spitzlbergerj/CaravanPi/circuit-board/V5/README.md

Die Dateien für die Bestellung bei JLCPCB.com sind im Verzeichnis JLCPCB enthalten

# Verkabelung zum Raspberry Pi

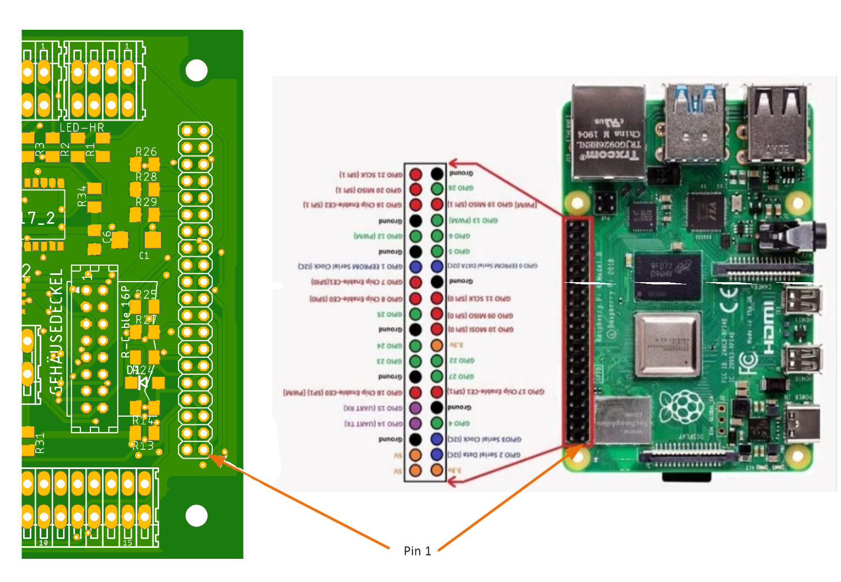
[picture p18: circuit-board/V5/CaravanPiPlatine-V5-Verbindung-RPi.png]
Verkabelung
