spitzlbergerj/CaravanPi/circuit-board/V3/README.md

# Platine Version 3

Diese Platinen-Version nutzt SMD Bauteile für alle Widerstände, Kondensatoren, Dioden und ICs **mit Ausnahme des P82B715P I2C Extender Chips**. Dieser ist hier als bedrahtete Version vorgesehen

## Platinen Layout
Oberseite  
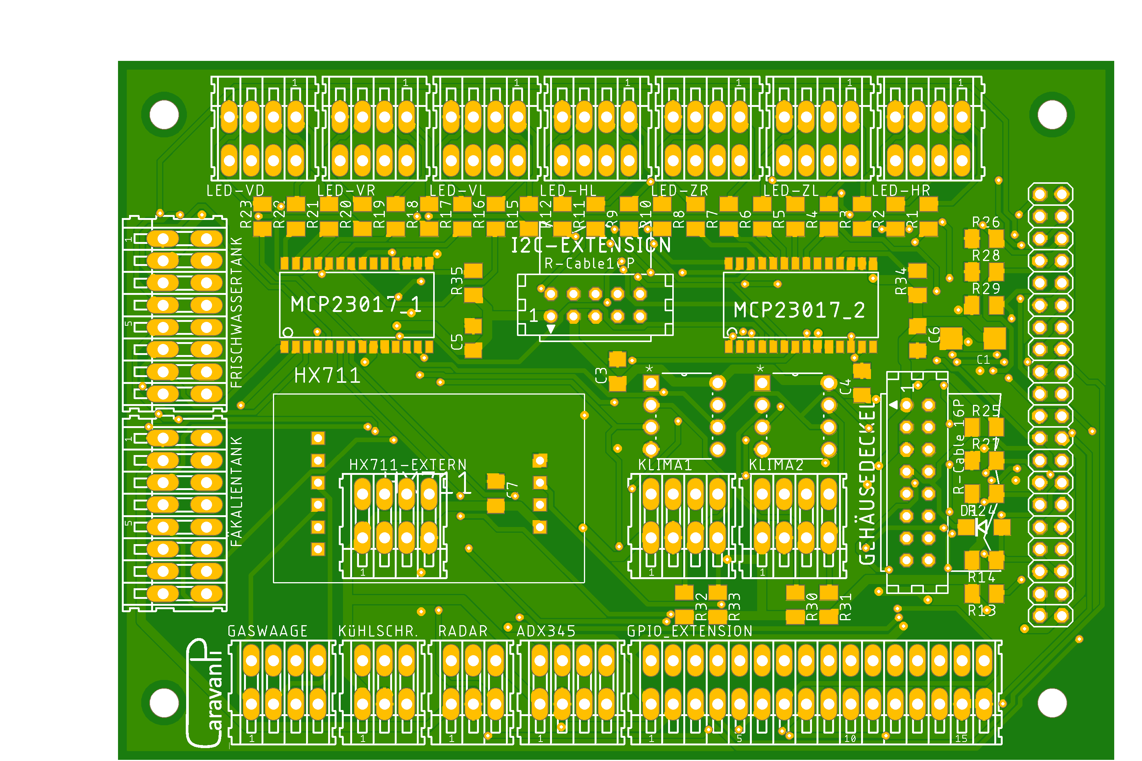
[picture p19: circuit-board/V3/CaravanPi-Platine-V3-Oberseite.png]
CaravanPi Platine V3 Oberseite
  

Unterseite  
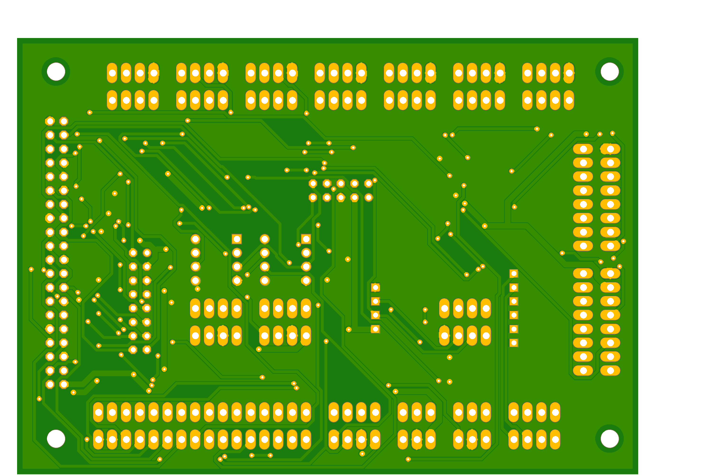
[picture p20: circuit-board/V3/CaravanPi-Platine-V3-Unterseite.png]
CaravanPi Platine V3 Unterseite
  

Bestückungslayout  
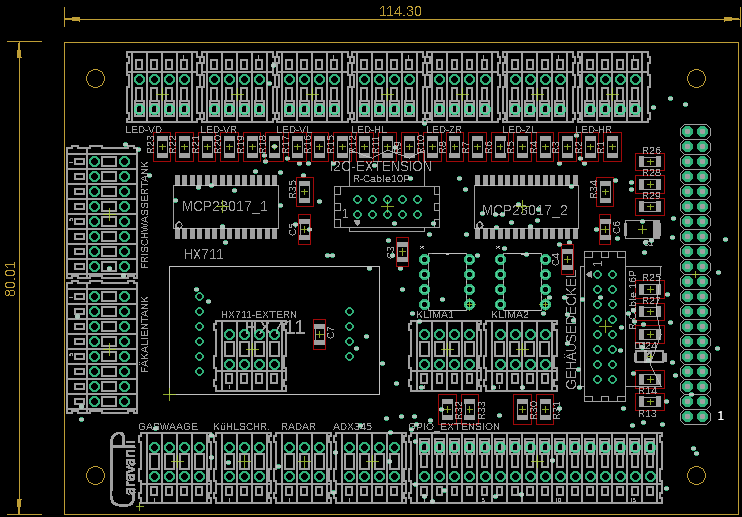
[picture p21: circuit-board/V3/CaravanPi-Platine-V3-Layout1.png]
CaravanPi Platine V3 Bestückungslayout
  

Bohrungen  
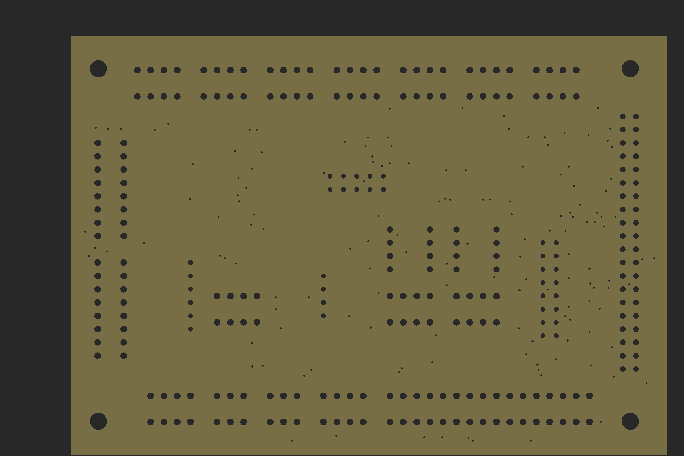
[picture p22: circuit-board/V3/CaravanPi-Platine-V3-Bohrungen.png]
CaravanPi Platine V3 Bohrungen
  

## Handbestückte Platine - Platine gefertigt in EU

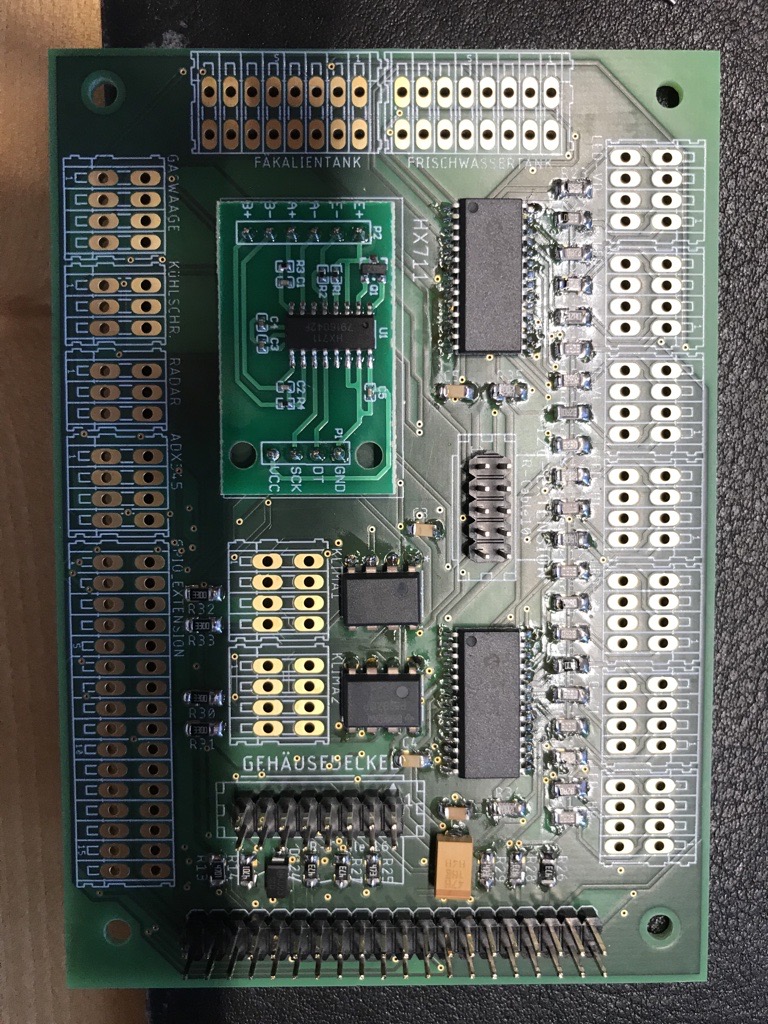
[picture p23: circuit-board/V3/CaravanPi-Platine-V3-EU-SMD-bestueckt.jpg]
CaravanPi Platine V3 EU per Hand bestückt
  

## JLCPCB Platine maschinell bestückt

CaravanPi Platine JLCPCB SMT bestückt  

Alle für die Bestellung bei JLCPCB.com benötigten dateien finden Sie im Unterverzeichnis [JLCPCB](JLCPCB)

## Bauteile Liste
In der Exceltabelle finden Sie alle benötigten Bauteile
