spitzlbergerj/CaravanPi/circuit-board/V4/README.md

# Platine Version 4

Diese Platinen Version nutzt SMD Bauteile für alle Widerstände, Kondensatoren, Dioden und ICs inkl. P82B715P I2C Extender Chips. Damit kann diese Platinenversion z. B. bei JLCPCB vollständig gefertigt werden, so dass nur noch Stecker und Klemmen manuell gelötet werden müssen.

## Platinen Layout
Oberseite  
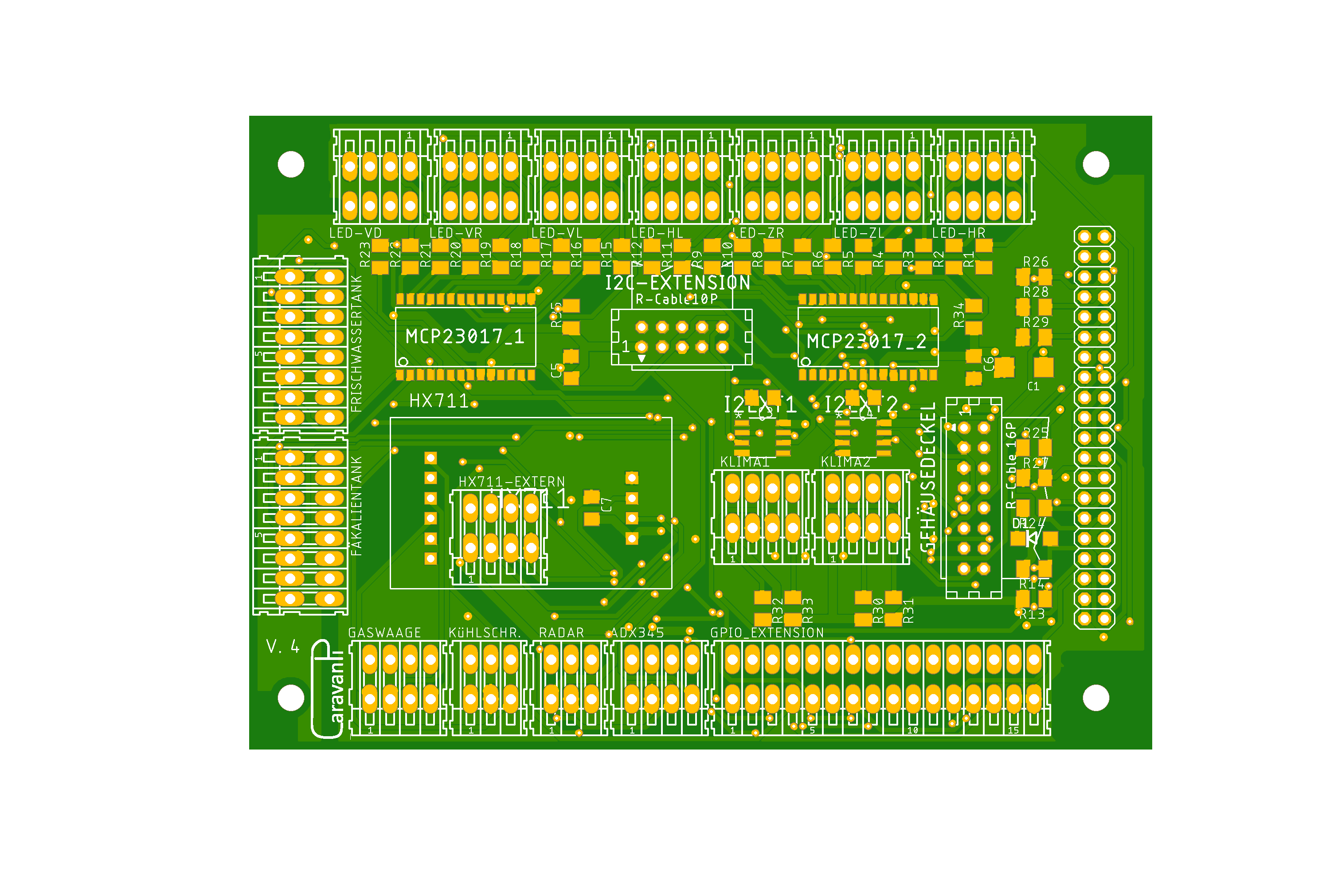
[picture p24: circuit-board/V4/CaravanPi-Platine-V4-Vorderseite.png]
CaravanPi Platine V4 Oberseite
  

Unterseite  
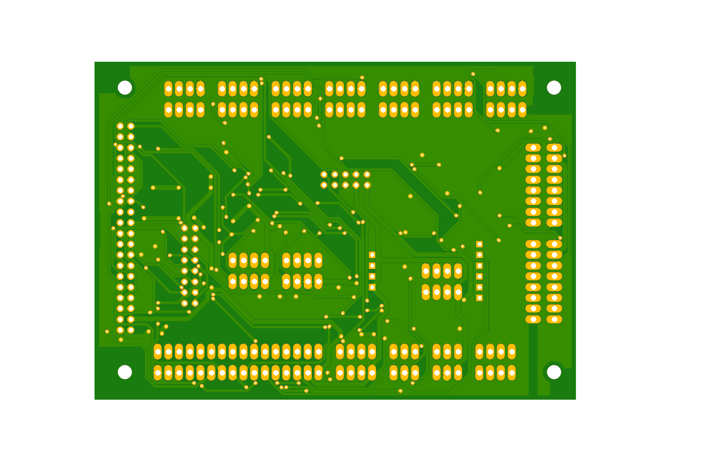
[picture p25: circuit-board/V4/CaravanPi-Platine-V4-Rueckseite.png]
CaravanPi Platine V4 Unterseite
  

Bestückungslayout  
CaravanPi Platine V4 Bestückungslayout  

Bohrungen  
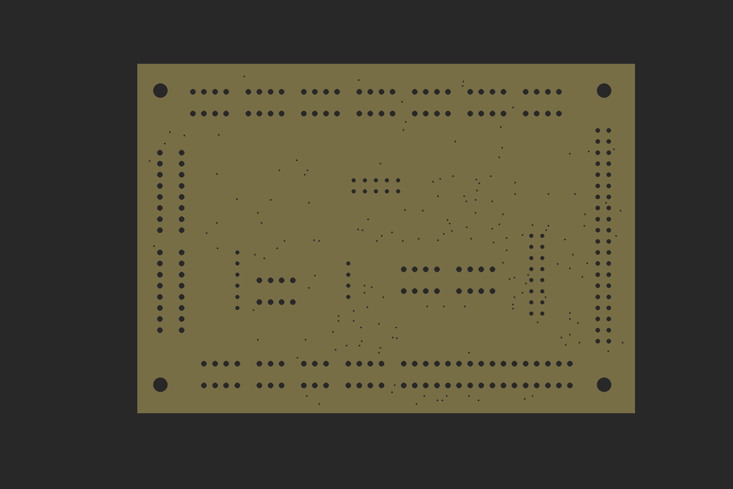
[picture p26: circuit-board/V4/CaravanPi-Platine-V4-Bohrungen.png]
CaravanPi Platine V4 Bohrungen
  

## JLCPCB Platine maschinell bestückt

CaravanPi Platine JLCPCB SMT bestückt  

Alle für die Bestellung bei JLCPCB.com benötigten dateien finden Sie im Unterverzeichnis [JLCPCB](JLCPCB)

## Bauteile Liste
In der Exceltabelle finden Sie alle benötigten Bauteile
