spitzlbergerj/CaravanPi/circuit-board/V5/JLCPCB/README.md

Dateien für die Bestellung bei JLCPCB.com

Teile Liste Stand 19.02.2023, inzwischen geändert, siehe neuestes BOM File

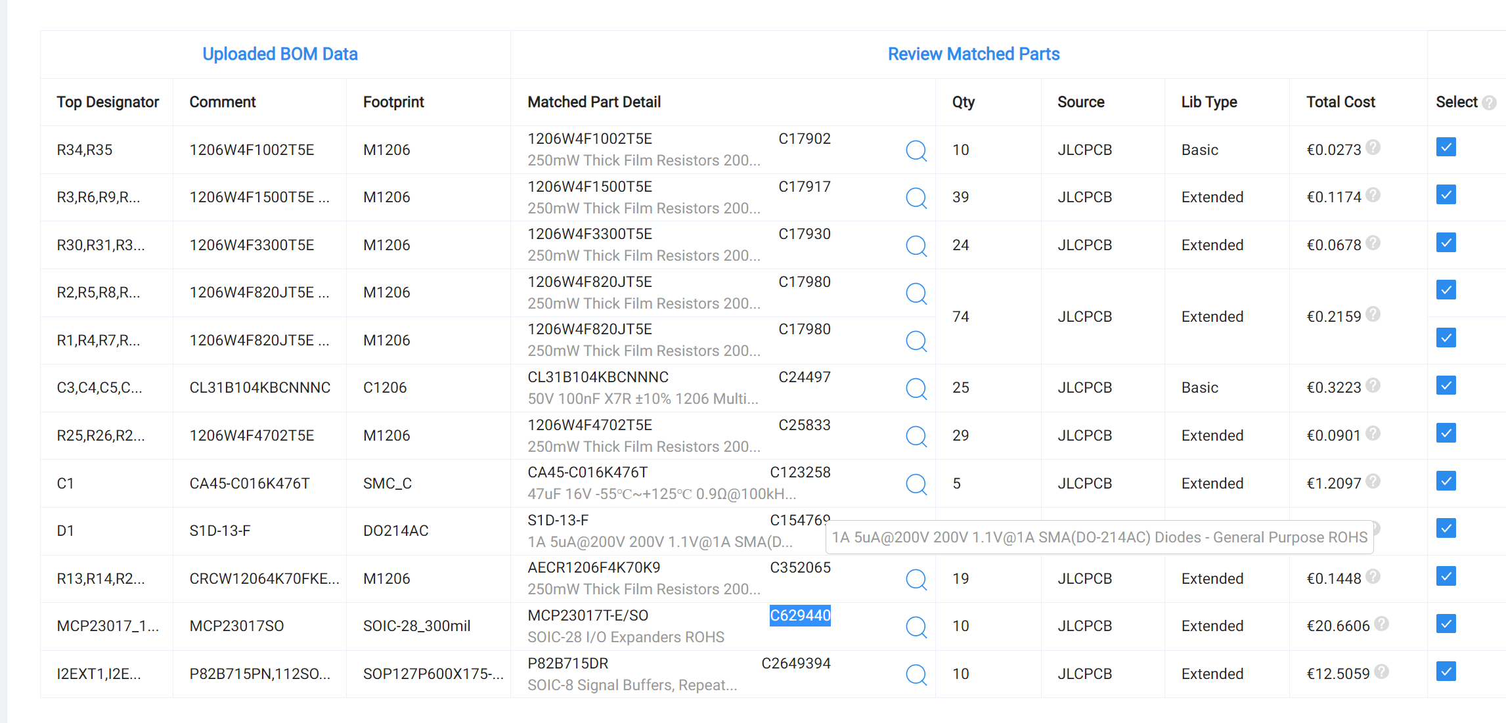
[picture p27: circuit-board/V5/JLCPCB/part-List-2023-02-23 083711.png]
 

Positionierung auf Platine

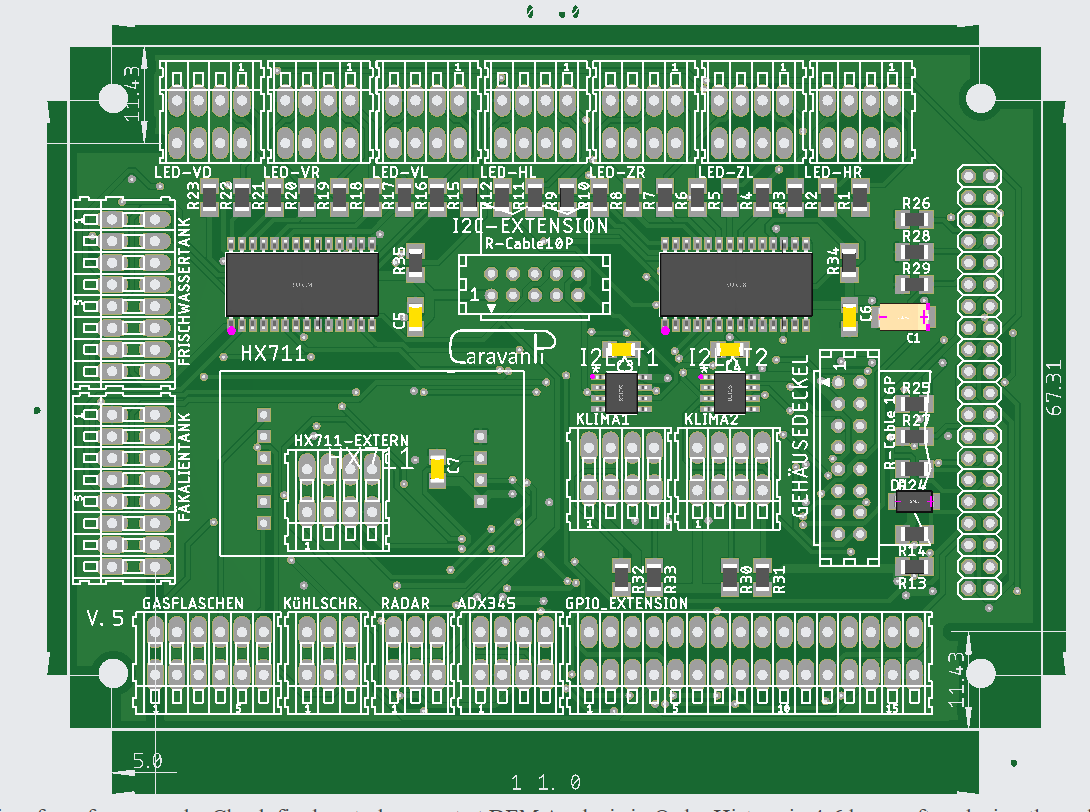
[picture p28: circuit-board/V5/JLCPCB/part-placement-2023-04-11.png]
