spitzlbergerj/CaravanPi/circuit-board/V3/JLCPCB/README.md

Dateien für die bestellung einer SMT bestückten Platine bei JLCPCB.com
