spitzlbergerj/CaravanPi/CaravanPi-Gesamt-Schaltplan.png

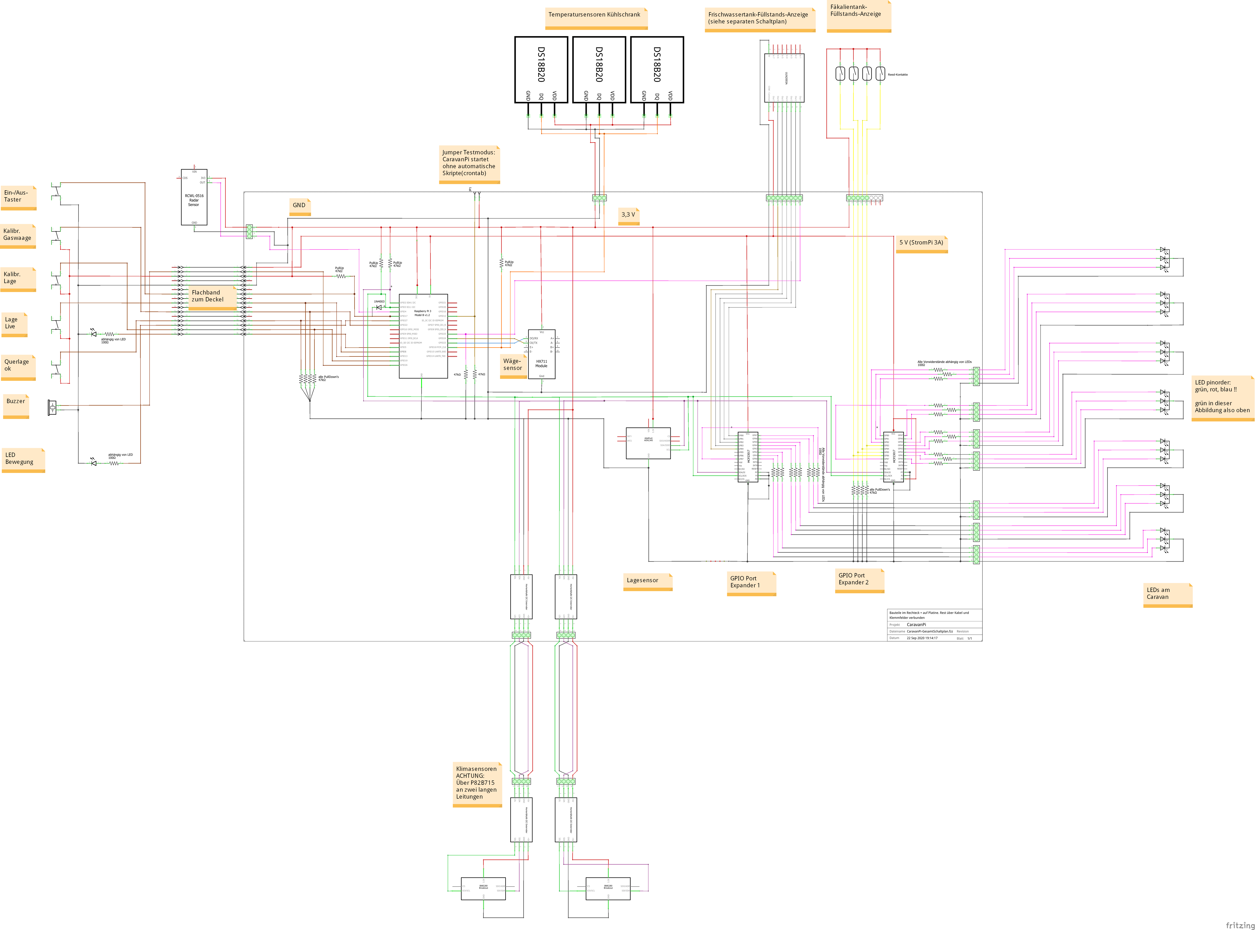
CaravanPi-Gesamt-Schaltplan.png
