spitzlbergerj/CaravanPi/circuit-board/V6/CaravanPi_V6_mit_Masse.png

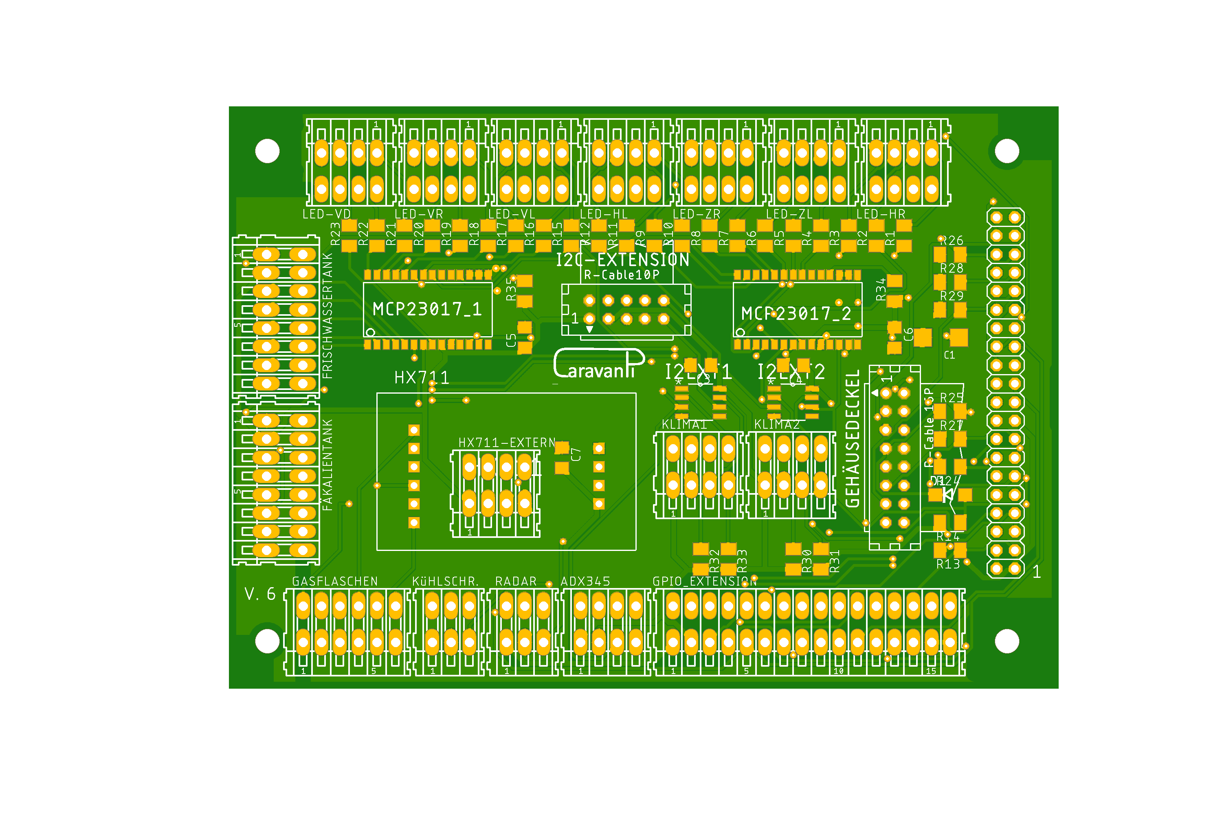
circuit-board/V6/CaravanPi_V6_mit_Masse.png
