spitzlbergerj/CaravanPi/images/CaravanPi_Steckplatine.png

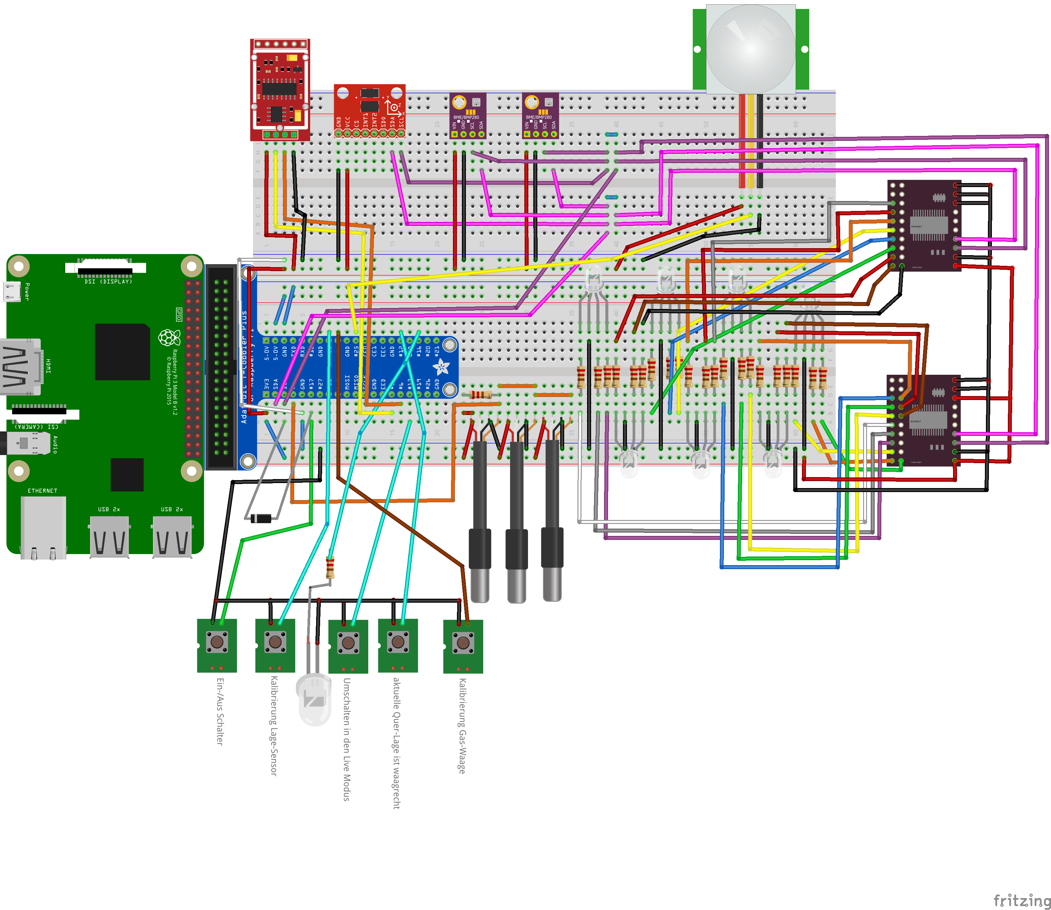
images/CaravanPi_Steckplatine.png
