spitzlbergerj/CaravanPi/images/doku/CaravanPi-Board-ADXL345.jpg

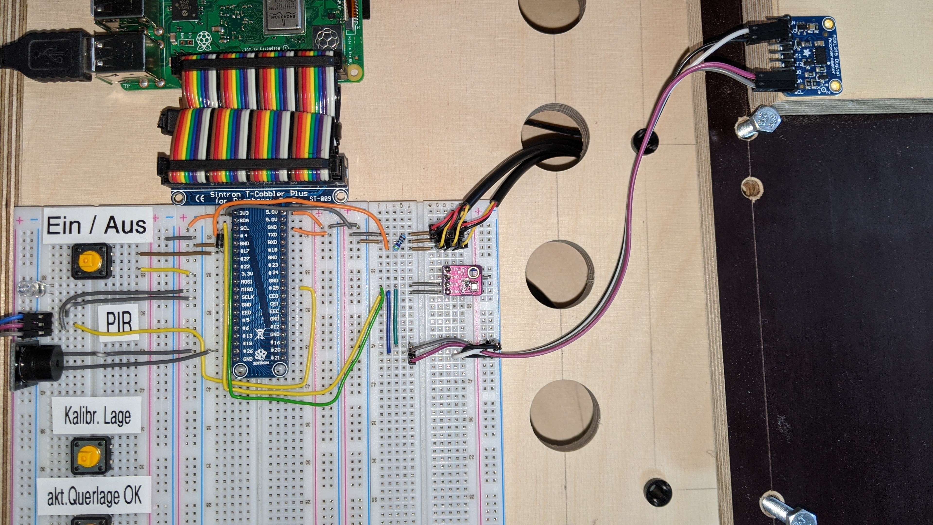
images/doku/CaravanPi-Board-ADXL345.jpg
