spitzlbergerj/CaravanPi/images/doku/CaravanPi-Board-BME280.jpg

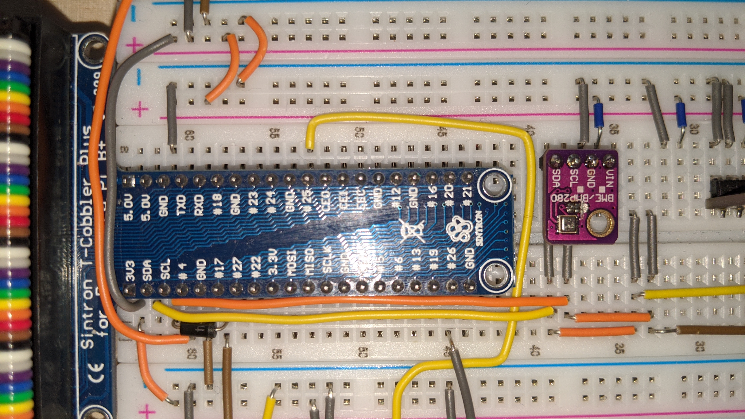
images/doku/CaravanPi-Board-BME280.jpg
