spitzlbergerj/CaravanPi/images/doku/CaravanPi-Board-div-taster.jpg

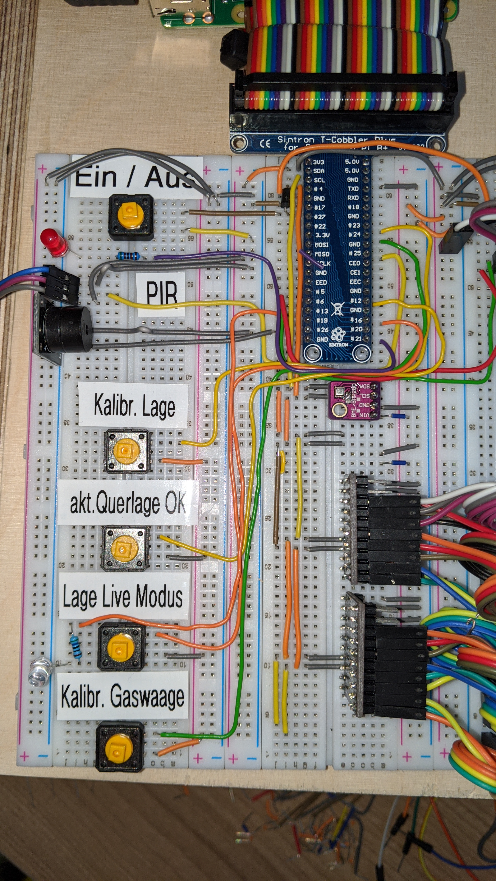
images/doku/CaravanPi-Board-div-taster.jpg
