spitzlbergerj/CaravanPi/images/doku/CaravanPi-Board-DS18B20.jpg

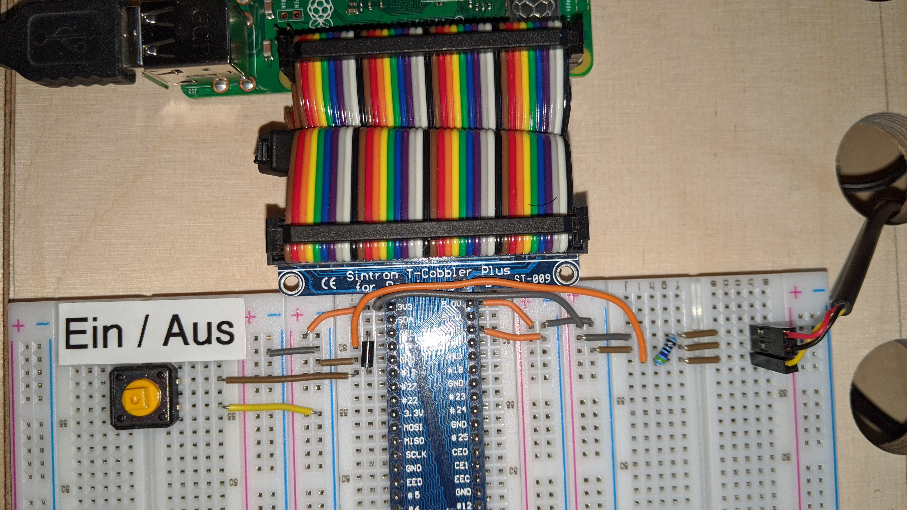
images/doku/CaravanPi-Board-DS18B20.jpg
