spitzlbergerj/CaravanPi/images/doku/CaravanPi-Board-HX711-1.jpg

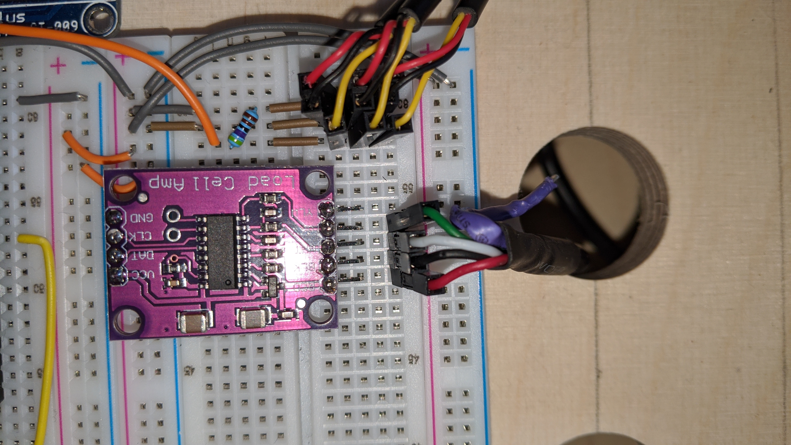
images/doku/CaravanPi-Board-HX711-1.jpg
