spitzlbergerj/CaravanPi/images/doku/CaravanPi-Board-HX711-2.jpg

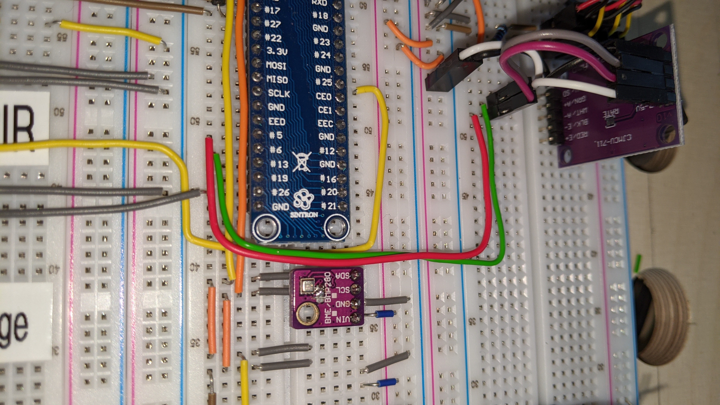
images/doku/CaravanPi-Board-HX711-2.jpg
