spitzlbergerj/CaravanPi/images/doku/CaravanPi-Board-MCP23017-1.jpg

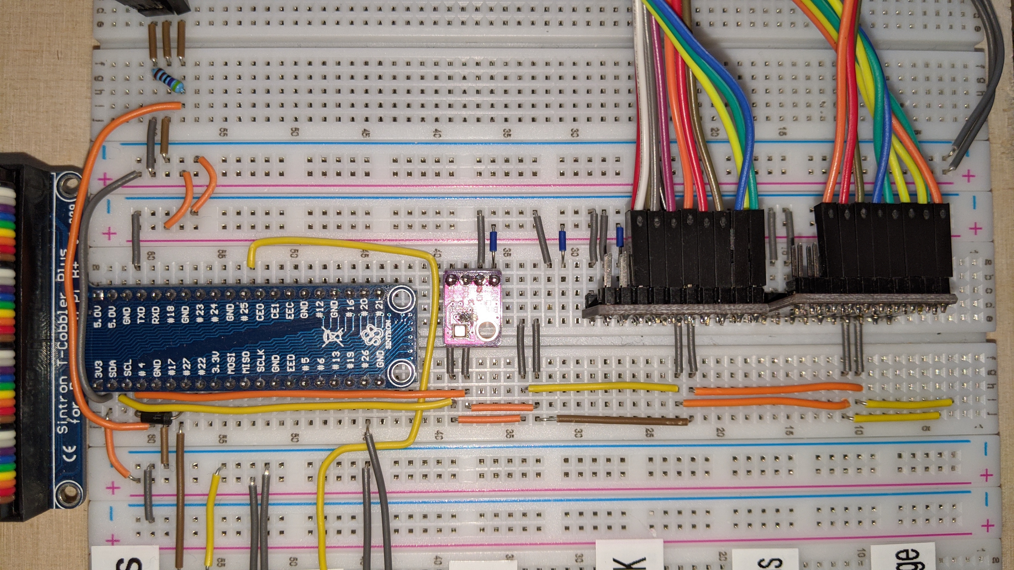
images/doku/CaravanPi-Board-MCP23017-1.jpg
