spitzlbergerj/CaravanPi/images/doku/CaravanPi-Board-MCP23017-2.jpg

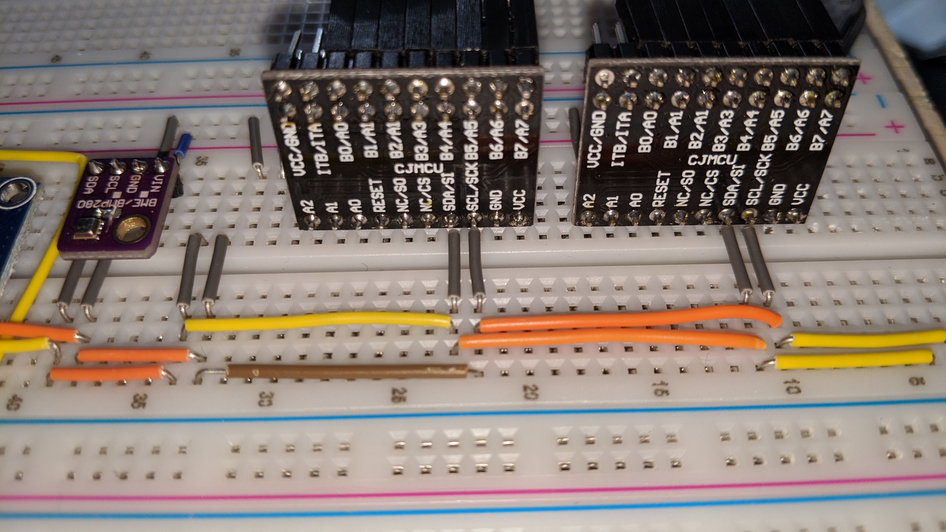
images/doku/CaravanPi-Board-MCP23017-2.jpg
