spitzlbergerj/CaravanPi/images/doku/CaravanPi-Board-OnOffSwitch.jpg

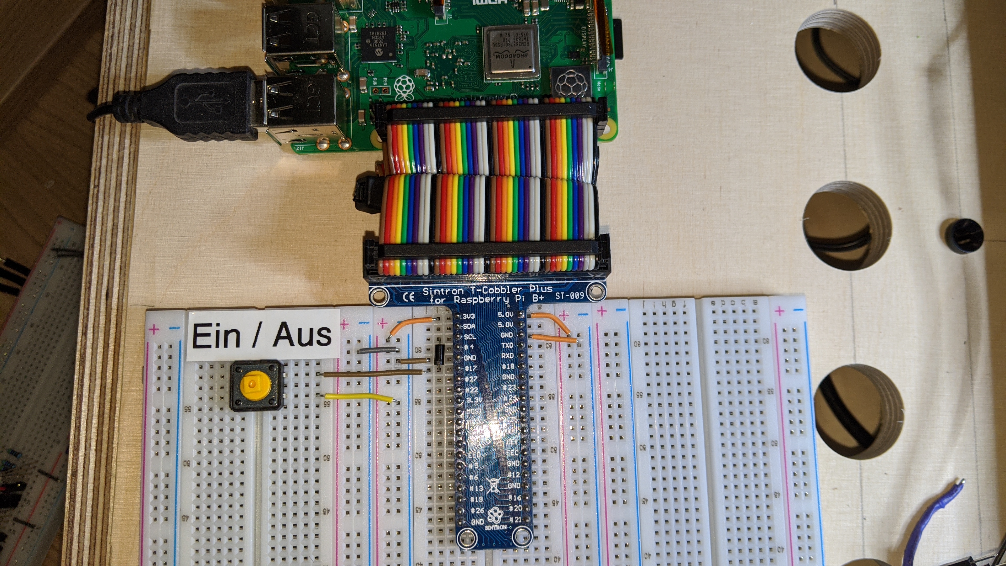
images/doku/CaravanPi-Board-OnOffSwitch.jpg
