spitzlbergerj/CaravanPi/images/doku/CaravanPi-Bodendurchlass-Kabel.jpg

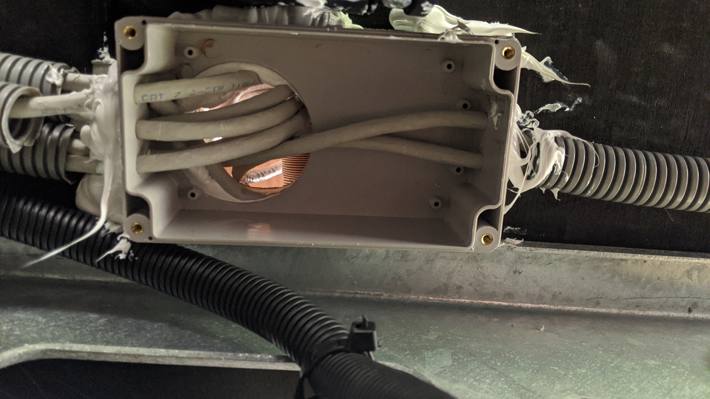
images/doku/CaravanPi-Bodendurchlass-Kabel.jpg
