spitzlbergerj/CaravanPi/images/doku/CaravanPi-config-website.jpg

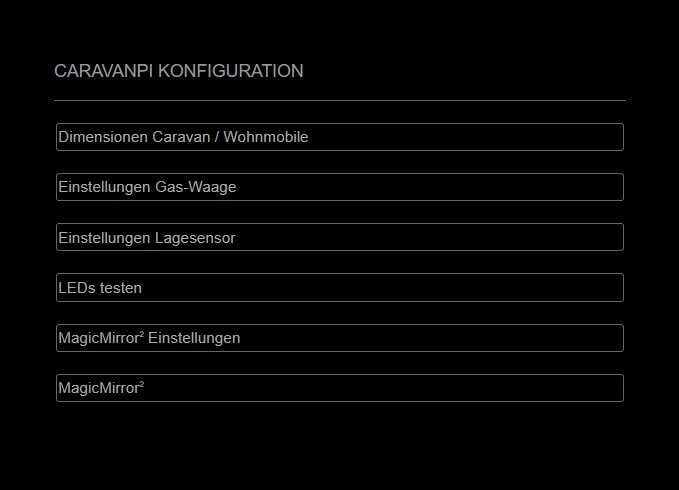
images/doku/CaravanPi-config-website.jpg
