spitzlbergerj/CaravanPi/images/doku/CaravanPi-Frischwasser-Schaltung-Gehäuse-1.jpg

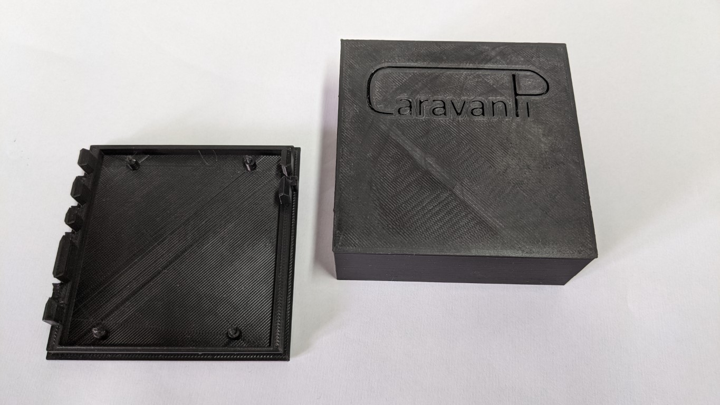
images/doku/CaravanPi-Frischwasser-Schaltung-Gehäuse-1.jpg
