spitzlbergerj/CaravanPi/images/doku/CaravanPi-Frischwasser-Schaltung-Gehäuse-2.jpg

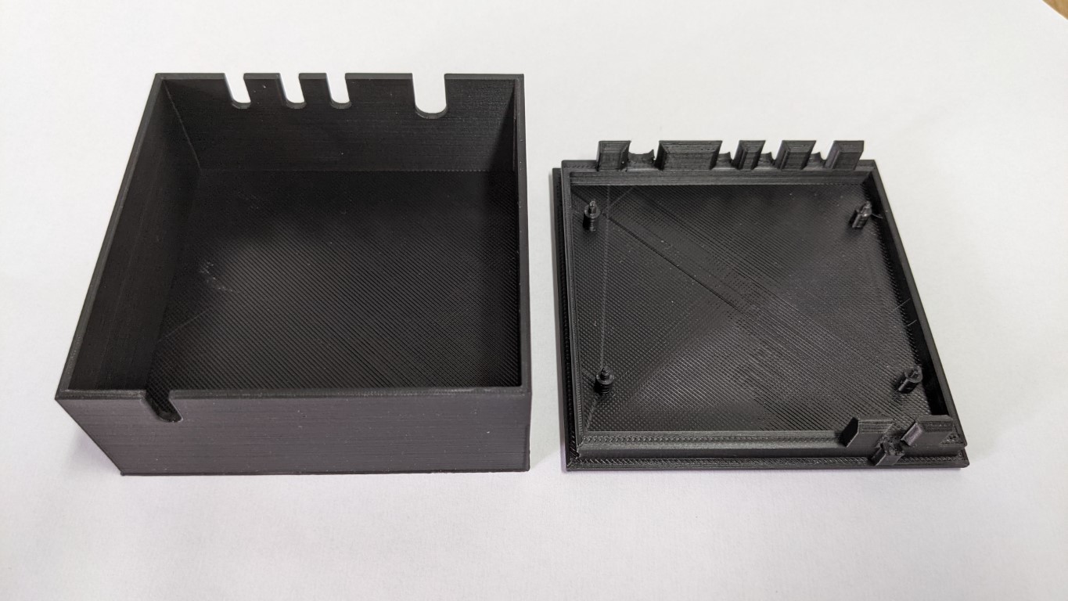
images/doku/CaravanPi-Frischwasser-Schaltung-Gehäuse-2.jpg
