spitzlbergerj/CaravanPi/images/doku/CaravanPi-Frischwasser-Schaltung-Gehäuse-3.jpg

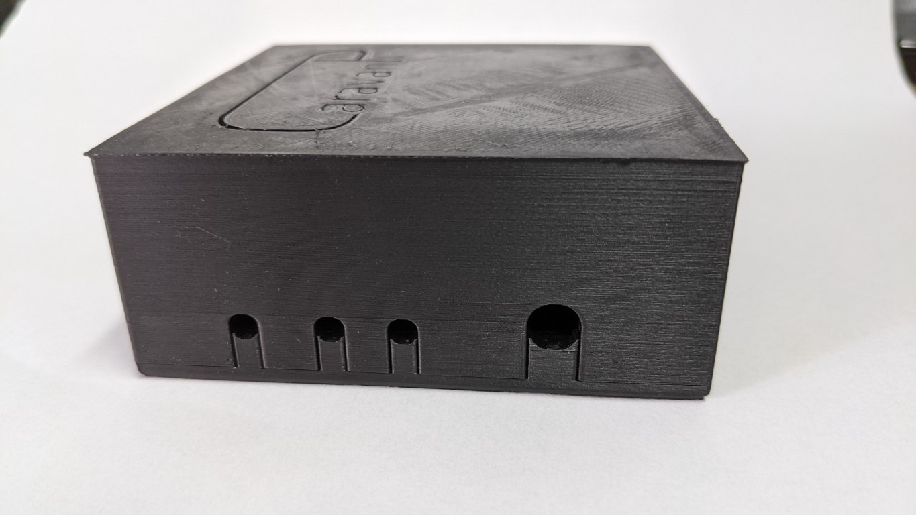
images/doku/CaravanPi-Frischwasser-Schaltung-Gehäuse-3.jpg
