spitzlbergerj/CaravanPi/images/doku/CaravanPi-Frischwasser-Schaltung-Gehäuse-4.jpg

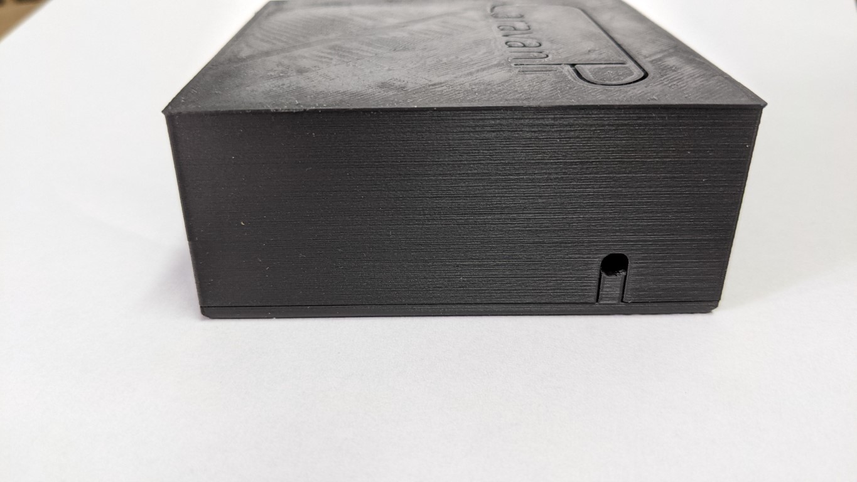
images/doku/CaravanPi-Frischwasser-Schaltung-Gehäuse-4.jpg
