spitzlbergerj/CaravanPi/images/doku/CaravanPi-Frischwasser-Schaltung-Gehäuse-5.jpg

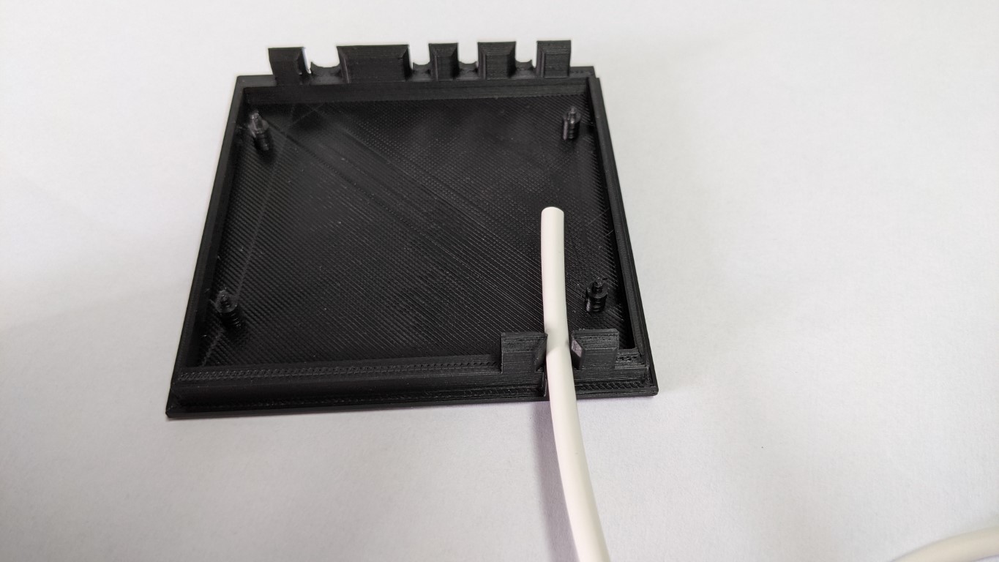
images/doku/CaravanPi-Frischwasser-Schaltung-Gehäuse-5.jpg
