spitzlbergerj/CaravanPi/images/doku/CaravanPi-Frischwasser-Schaltung-Gehäuse-6.jpg

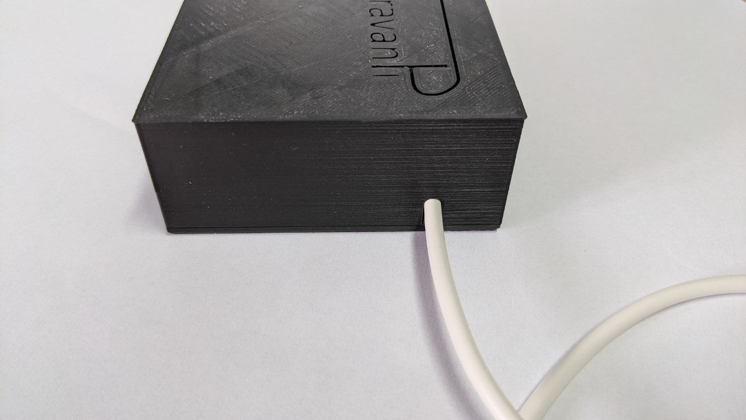
images/doku/CaravanPi-Frischwasser-Schaltung-Gehäuse-6.jpg
