spitzlbergerj/CaravanPi/images/doku/CaravanPi-Frischwassertank-Platine1.jpg

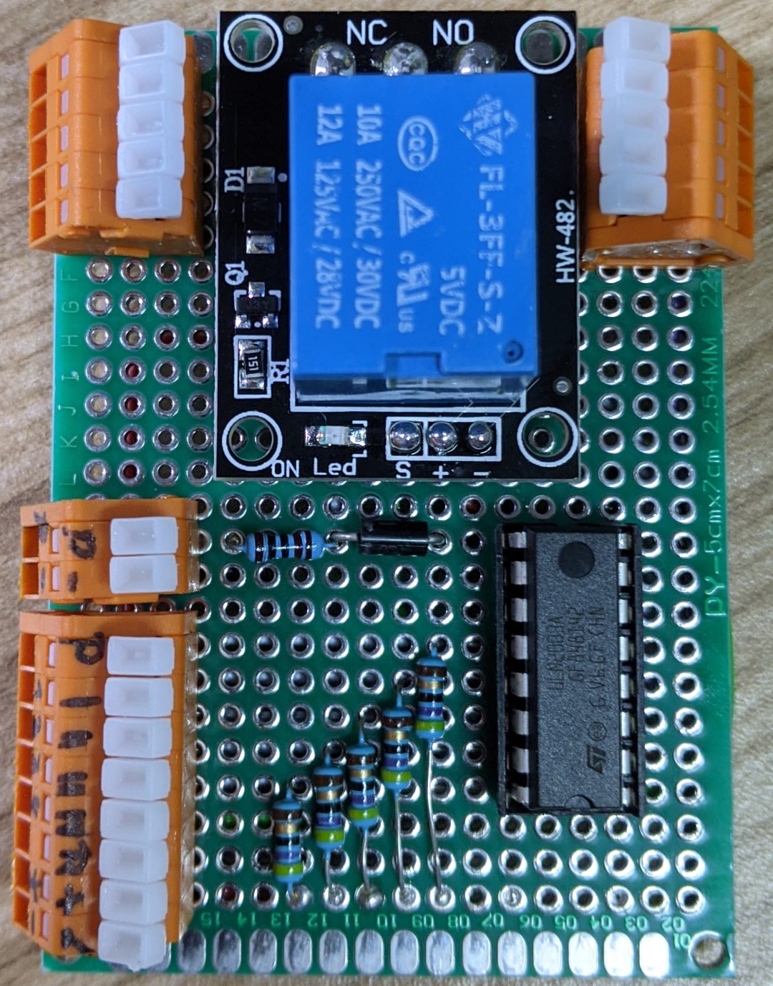
images/doku/CaravanPi-Frischwassertank-Platine1.jpg
