spitzlbergerj/CaravanPi/images/doku/CaravanPi-Frischwassertank-Platine2.jpg

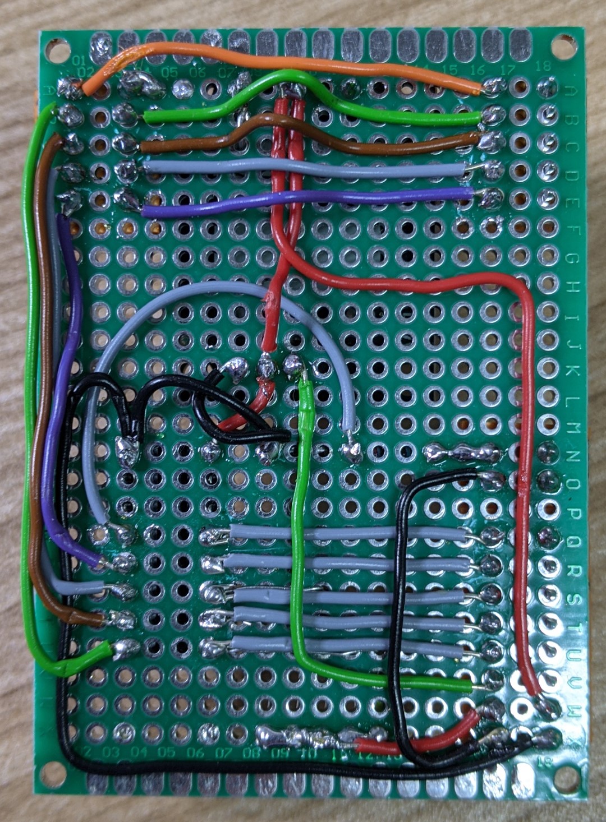
images/doku/CaravanPi-Frischwassertank-Platine2.jpg
