spitzlbergerj/CaravanPi/images/doku/CaravanPi-Frischwassertank-Schaltplan.png

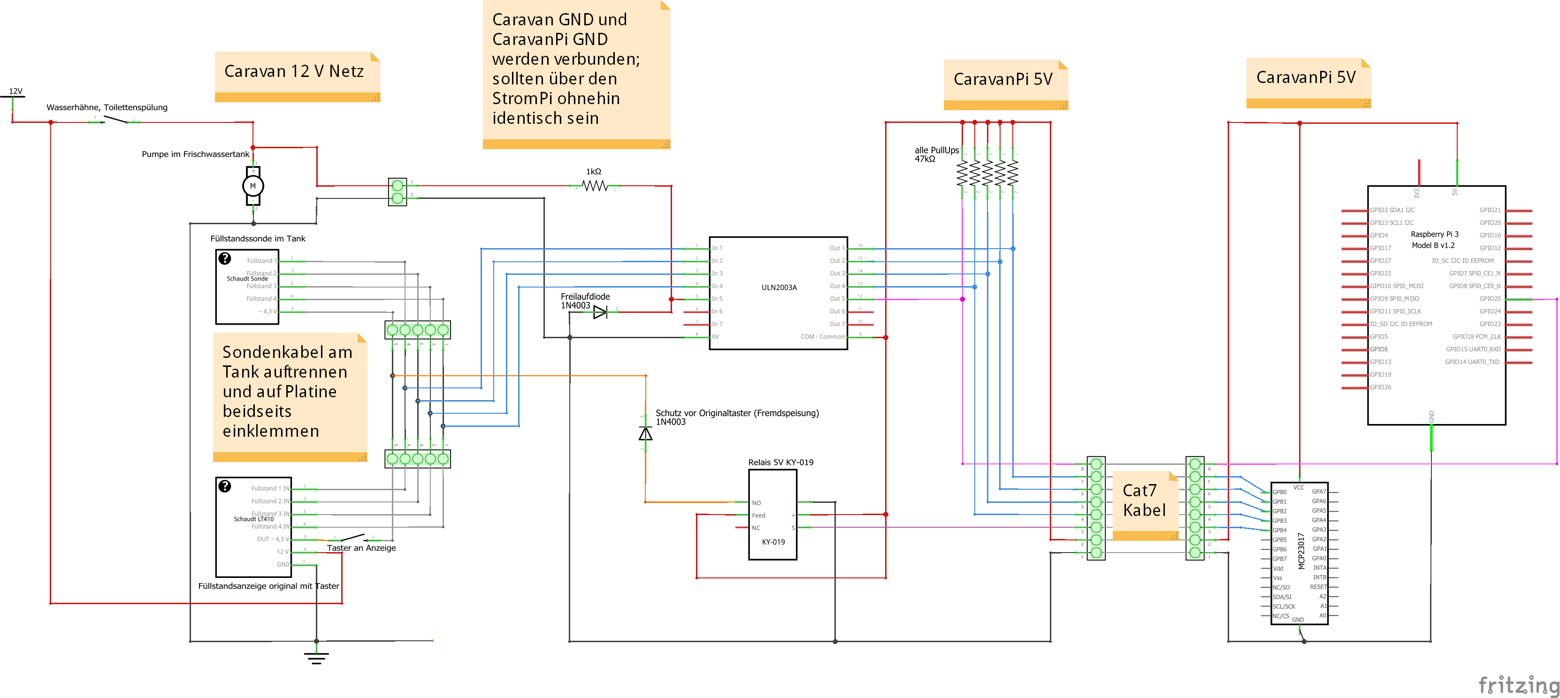
images/doku/CaravanPi-Frischwassertank-Schaltplan.png
