spitzlbergerj/CaravanPi/images/doku/CaravanPi-Fäkalientank-1.jpg

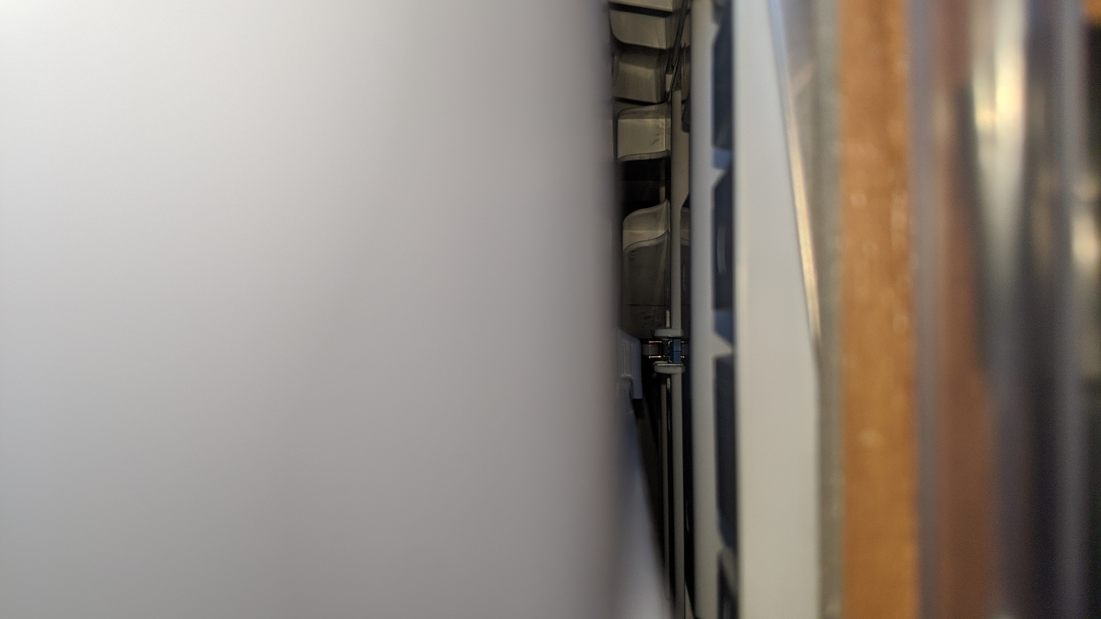
images/doku/CaravanPi-Fäkalientank-1.jpg
