spitzlbergerj/CaravanPi/images/doku/CaravanPi-Fäkalientank-Gehäuse-komplett.jpg

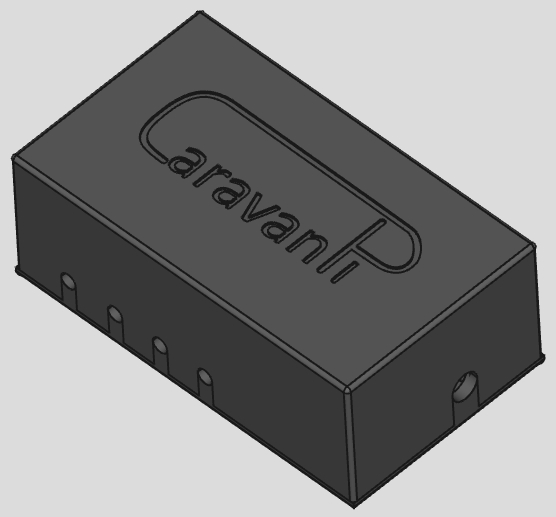
images/doku/CaravanPi-Fäkalientank-Gehäuse-komplett.jpg
