spitzlbergerj/CaravanPi/images/doku/CaravanPi-Fäkalientank-Gehäuse-Unterschale.jpg

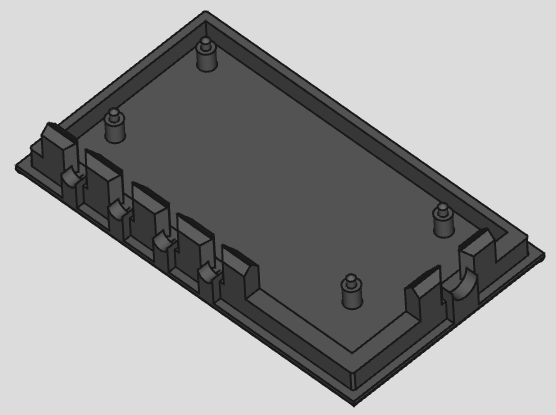
images/doku/CaravanPi-Fäkalientank-Gehäuse-Unterschale.jpg
