spitzlbergerj/CaravanPi/images/doku/CaravanPi-Fäkalientank-Original.jpg

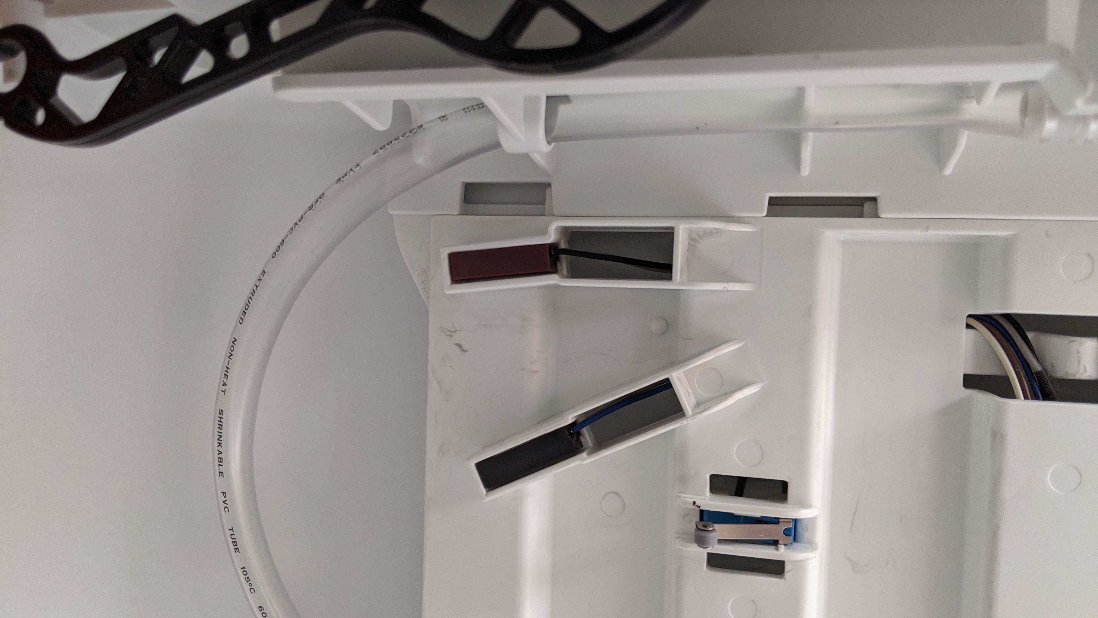
images/doku/CaravanPi-Fäkalientank-Original.jpg
