spitzlbergerj/CaravanPi/images/doku/CaravanPi-Fäkalientank-ReedKontakt-komplett1.jpg

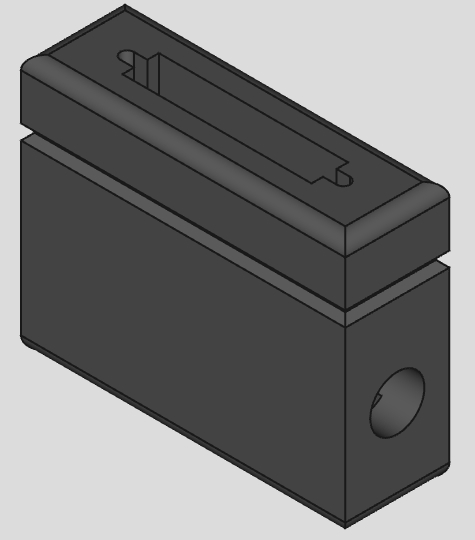
images/doku/CaravanPi-Fäkalientank-ReedKontakt-komplett1.jpg
