spitzlbergerj/CaravanPi/images/doku/CaravanPi-Fäkalientank-ReedKontakt-komplett2.jpg

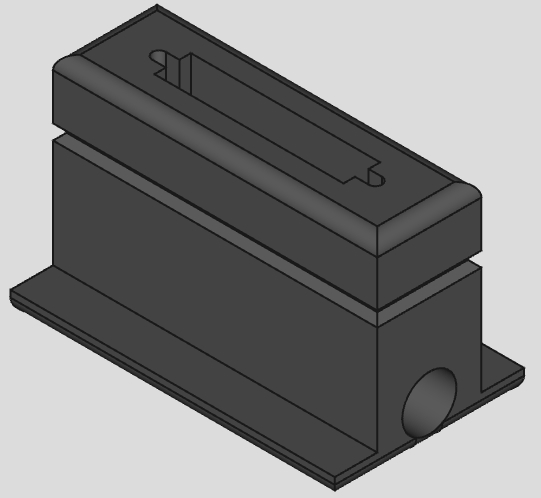
images/doku/CaravanPi-Fäkalientank-ReedKontakt-komplett2.jpg
