spitzlbergerj/CaravanPi/images/doku/CaravanPi-Fäkalientank-Schaltplan.png

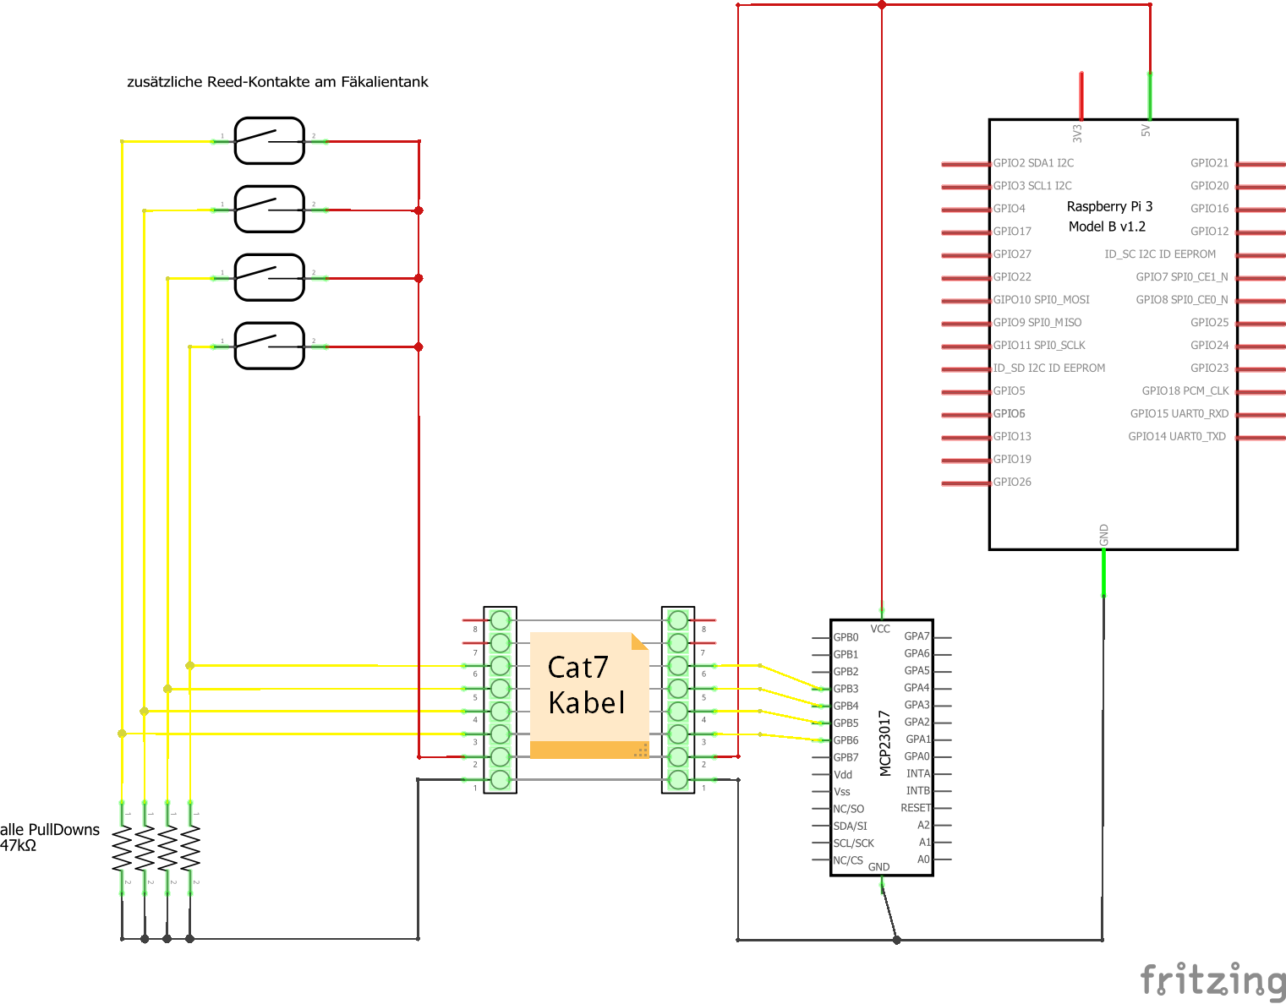
images/doku/CaravanPi-Fäkalientank-Schaltplan.png
