spitzlbergerj/CaravanPi/images/doku/CaravanPi-FäkTank-inkl-Maße.png

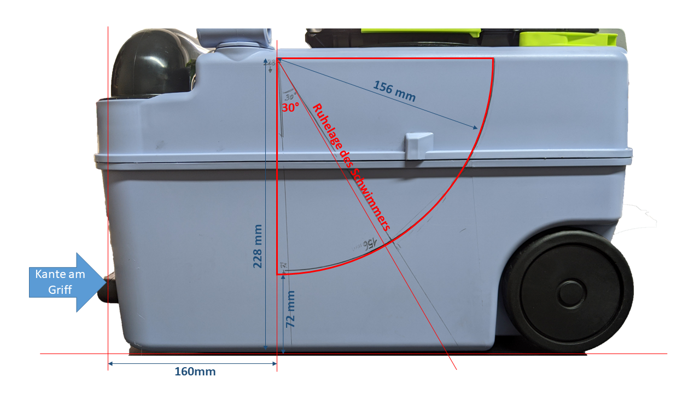
images/doku/CaravanPi-FäkTank-inkl-Maße.png
