spitzlbergerj/CaravanPi/images/doku/CaravanPi-FäkTank-nur-Maße.png

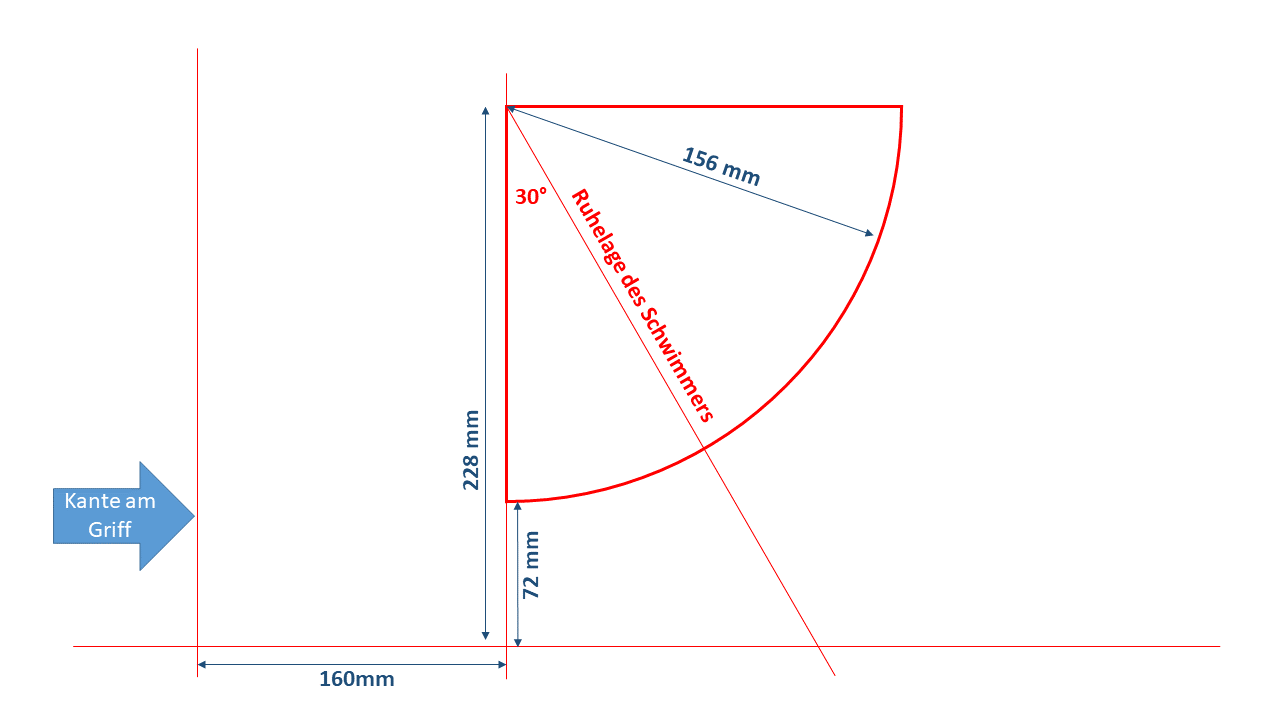
images/doku/CaravanPi-FäkTank-nur-Maße.png
