spitzlbergerj/CaravanPi/images/doku/CaravanPi-Gasflaschenwaage1.jpg

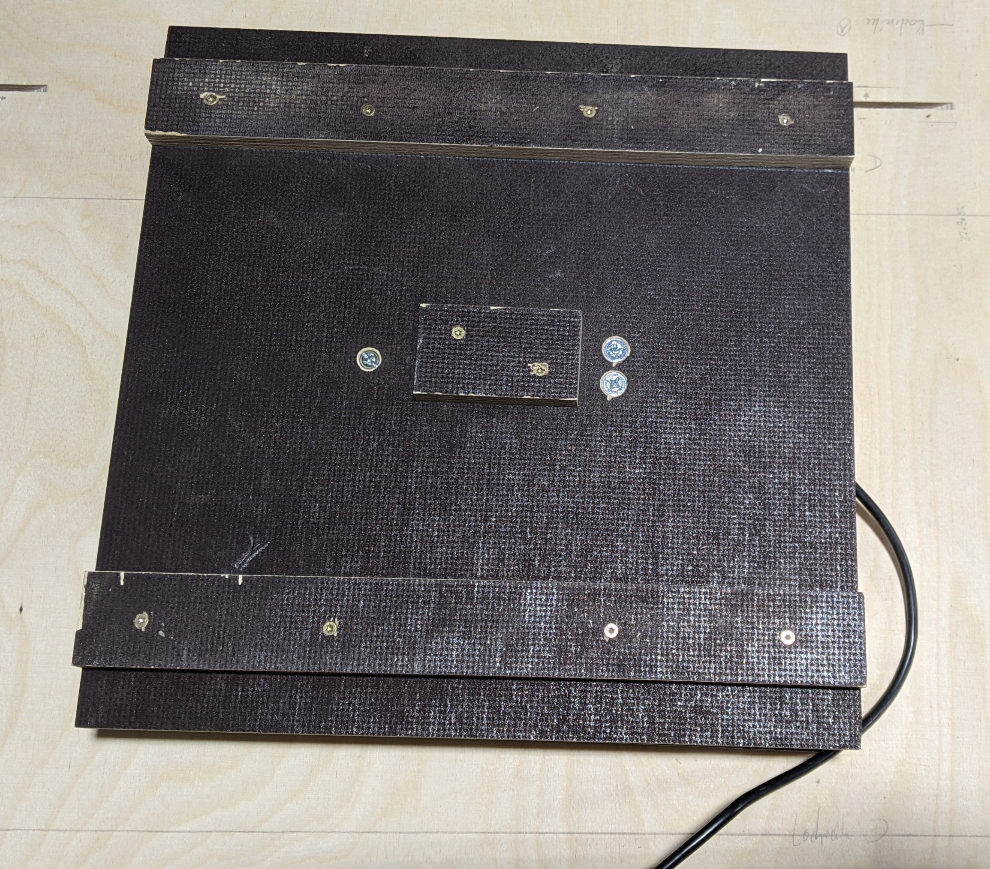
images/doku/CaravanPi-Gasflaschenwaage1.jpg
