spitzlbergerj/CaravanPi/images/doku/CaravanPi-Gasflaschenwaage2.jpg

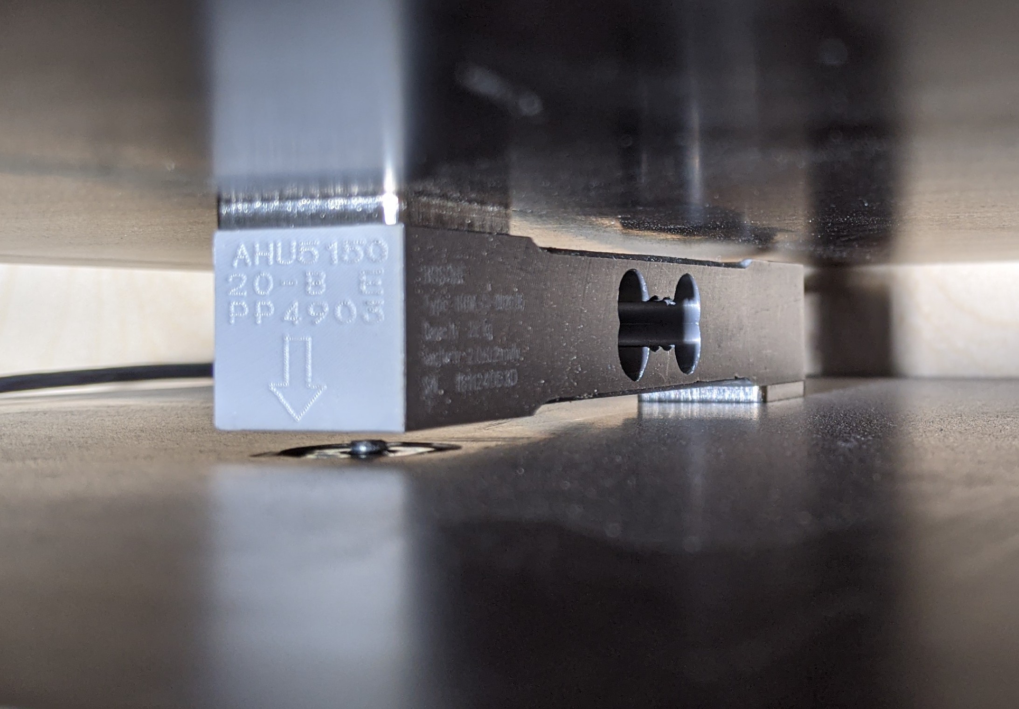
images/doku/CaravanPi-Gasflaschenwaage2.jpg
