spitzlbergerj/CaravanPi/images/doku/CaravanPi-Gasflaschenwaage3.jpg

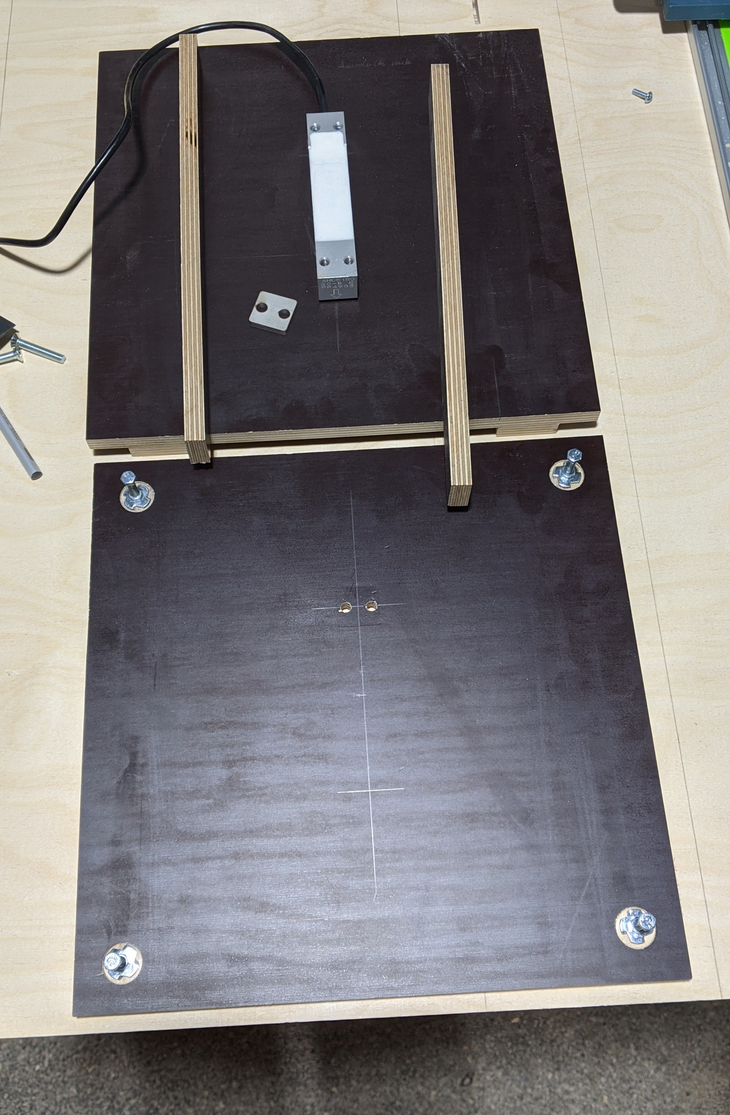
images/doku/CaravanPi-Gasflaschenwaage3.jpg
