spitzlbergerj/CaravanPi/images/doku/CaravanPi-Gasflaschenwaage4.jpg

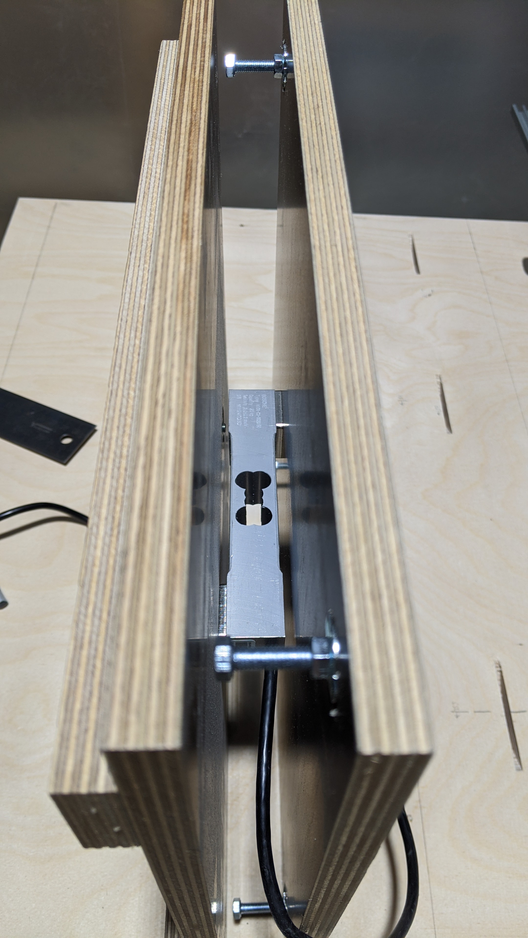
images/doku/CaravanPi-Gasflaschenwaage4.jpg
