spitzlbergerj/CaravanPi/images/doku/CaravanPi-Gasflaschenwaage.png

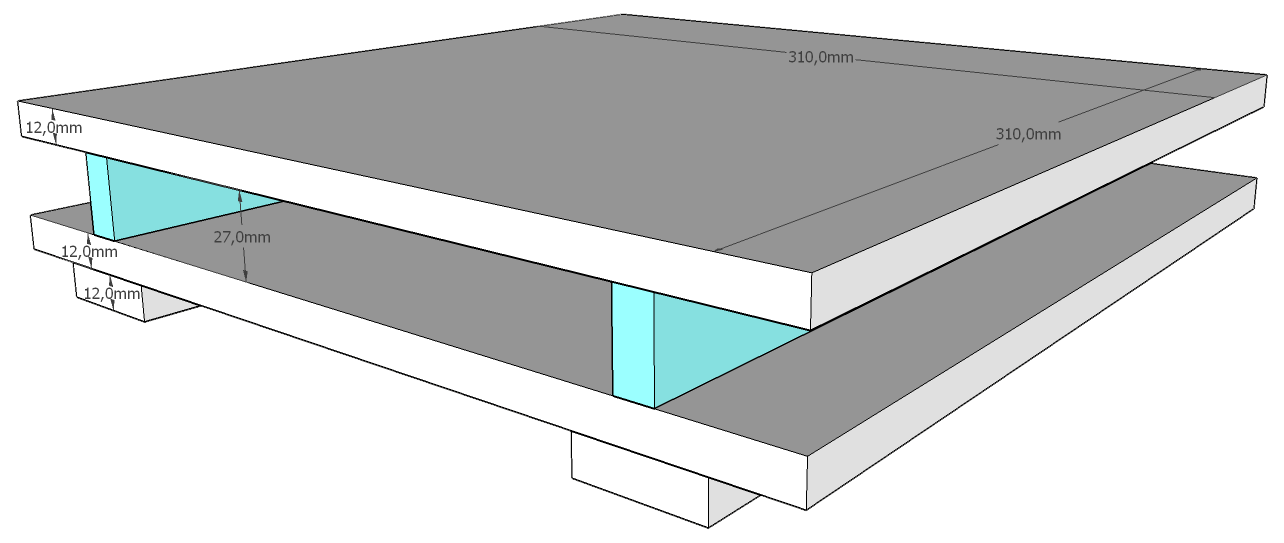
images/doku/CaravanPi-Gasflaschenwaage.png
