spitzlbergerj/CaravanPi/images/doku/CaravanPi-Gehaeuse1.jpg

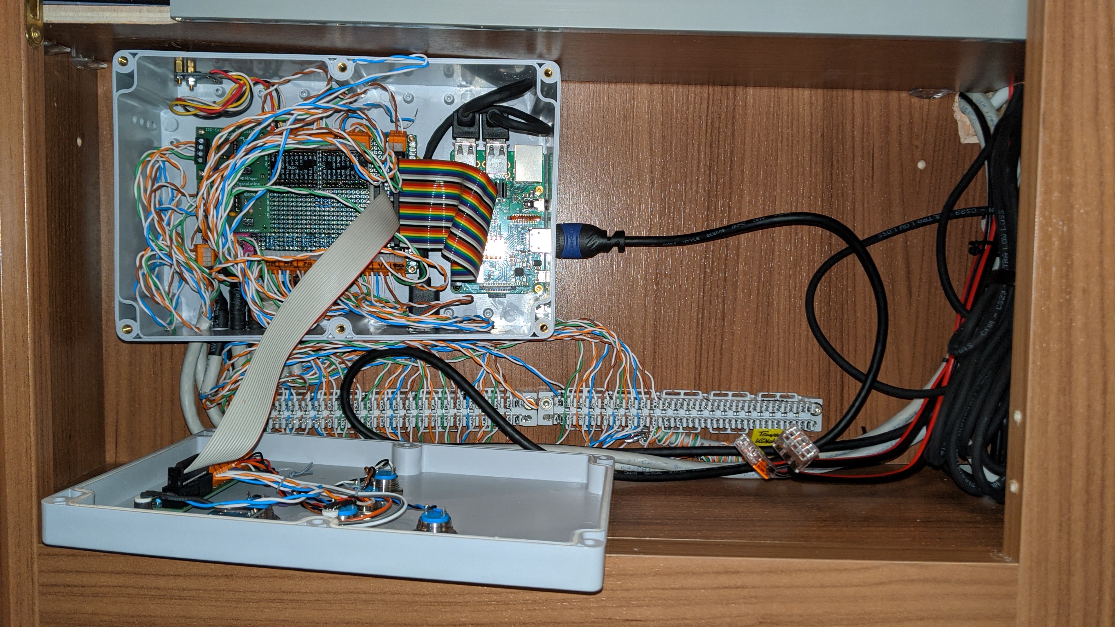
images/doku/CaravanPi-Gehaeuse1.jpg
