spitzlbergerj/CaravanPi/images/doku/CaravanPi-Gehaeuse2.jpg

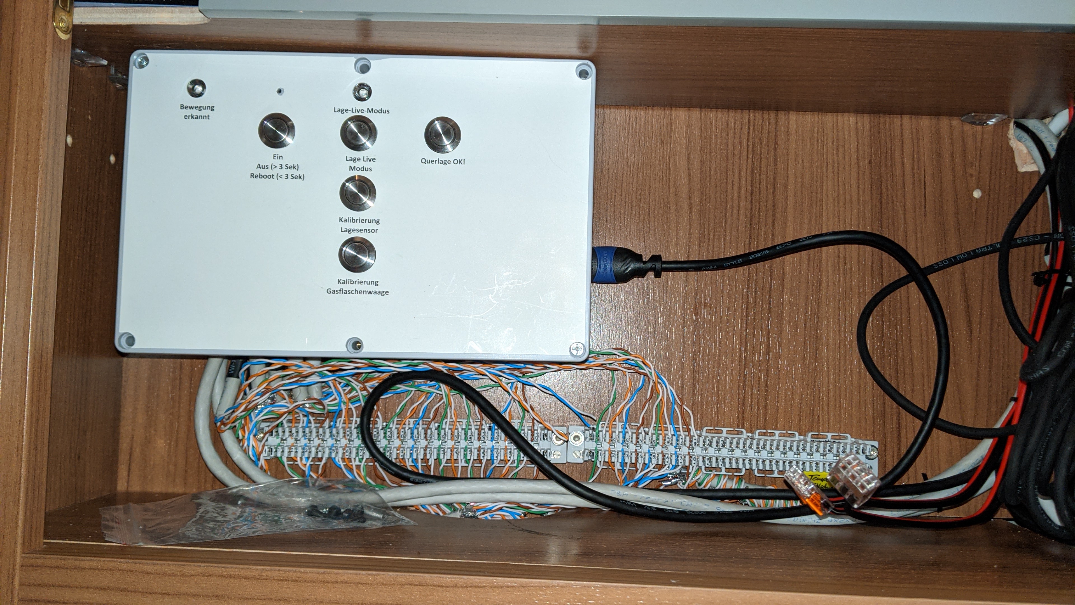
images/doku/CaravanPi-Gehaeuse2.jpg
