spitzlbergerj/CaravanPi/images/doku/CaravanPi-Gesamt-Schaltplan.png

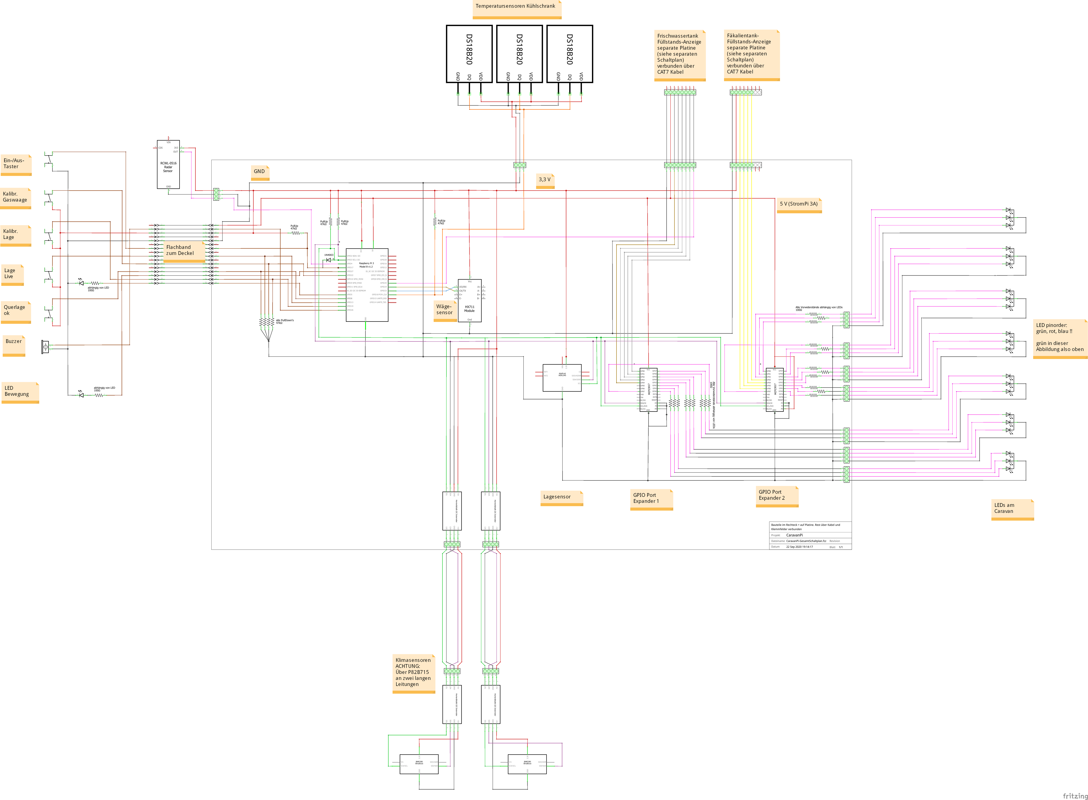
images/doku/CaravanPi-Gesamt-Schaltplan.png
