spitzlbergerj/CaravanPi/images/doku/CaravanPi-Gesamtschaltplan-Prinzip.png

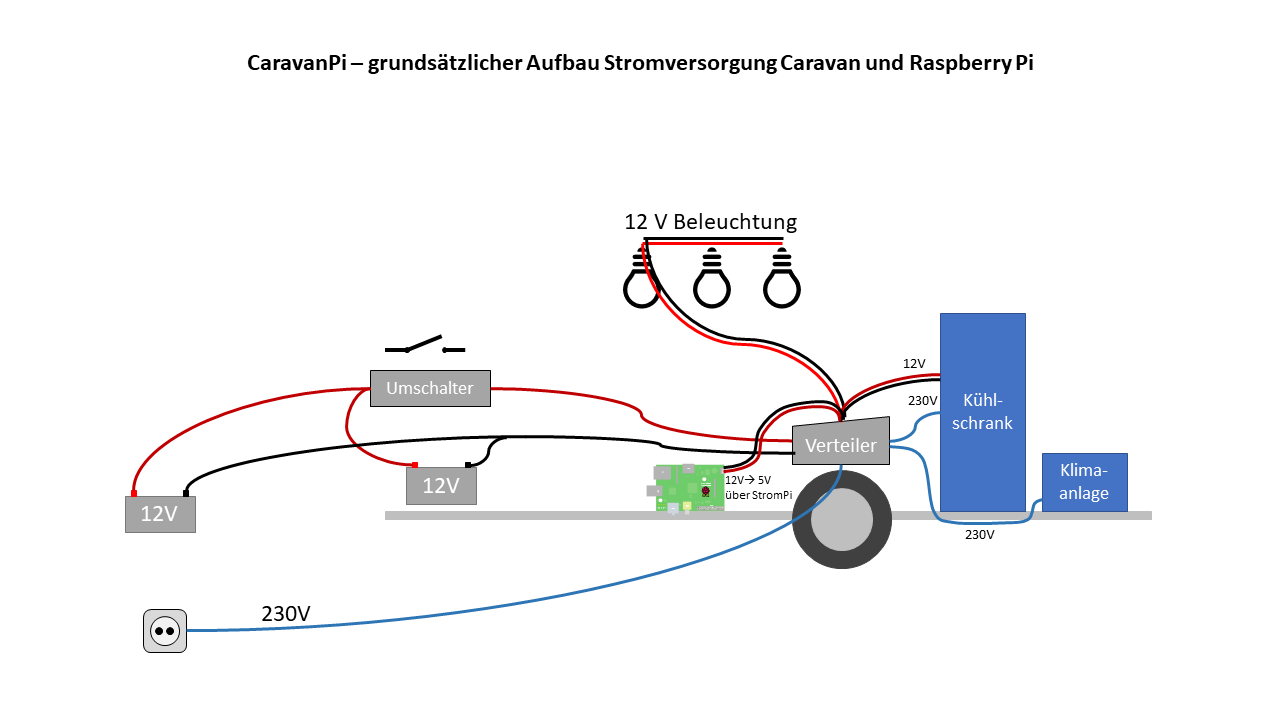
images/doku/CaravanPi-Gesamtschaltplan-Prinzip.png
