spitzlbergerj/CaravanPi/images/doku/CaravanPi-HX711-mehrere-Waegezellen.jpg

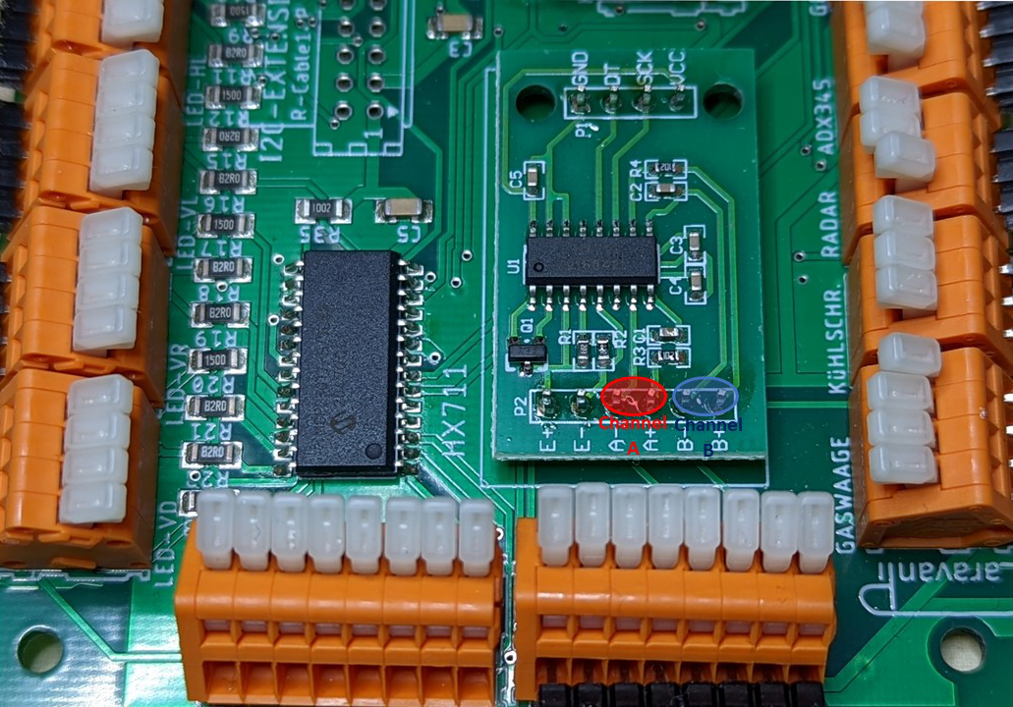
images/doku/CaravanPi-HX711-mehrere-Waegezellen.jpg
