spitzlbergerj/CaravanPi/images/doku/CaravanPi-I2C-Extender1.jpg

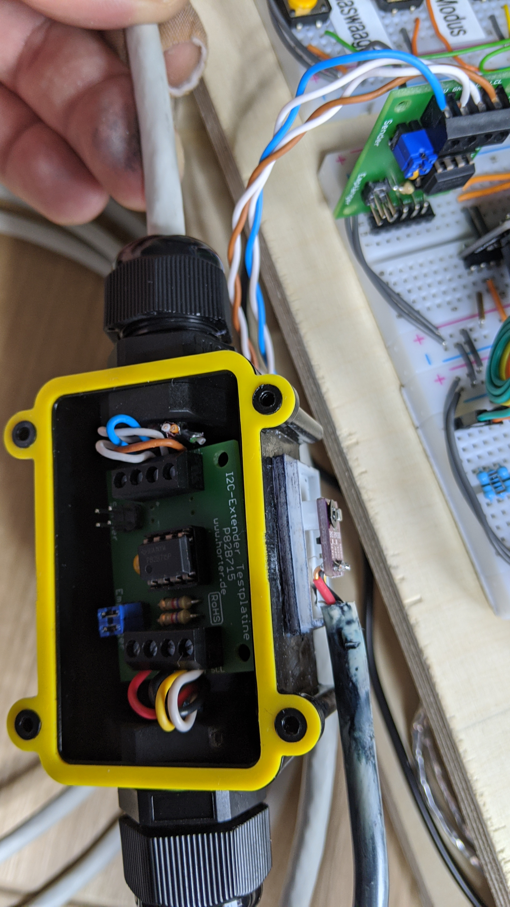
images/doku/CaravanPi-I2C-Extender1.jpg
