spitzlbergerj/CaravanPi/images/doku/CaravanPi-I2C-Extender2.jpg

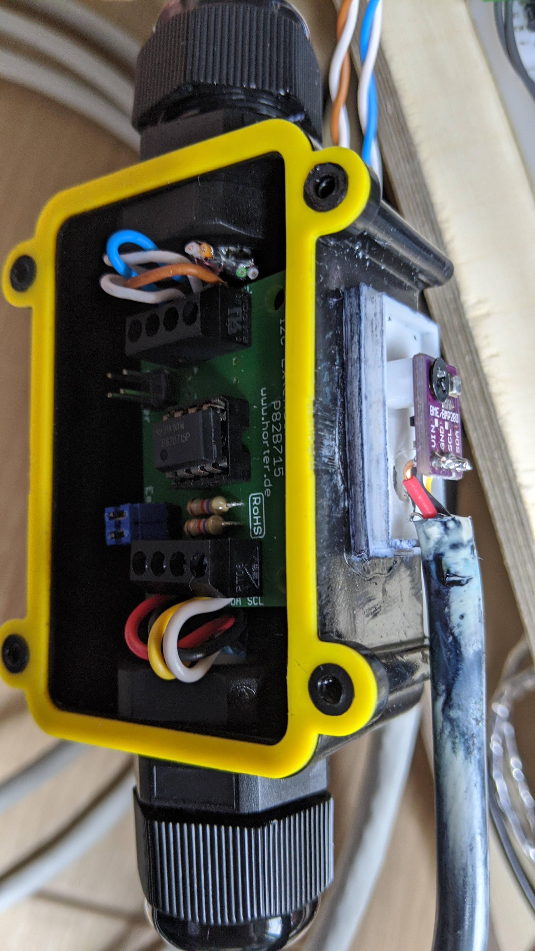
images/doku/CaravanPi-I2C-Extender2.jpg
