spitzlbergerj/CaravanPi/images/doku/CaravanPi-I2C-Extender3.jpg

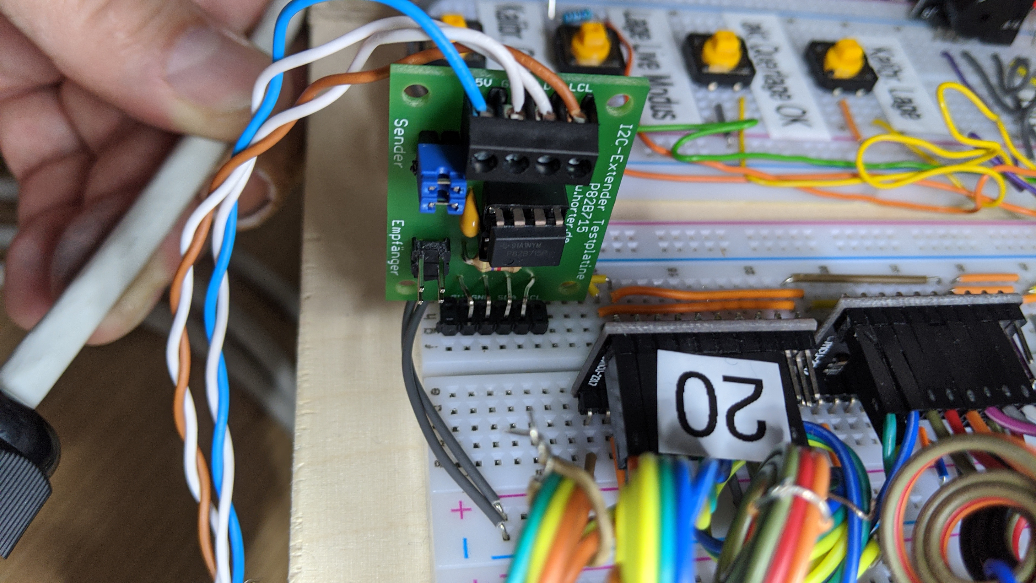
images/doku/CaravanPi-I2C-Extender3.jpg
