spitzlbergerj/CaravanPi/images/doku/CaravanPi-LED-Datasheet1.jpg

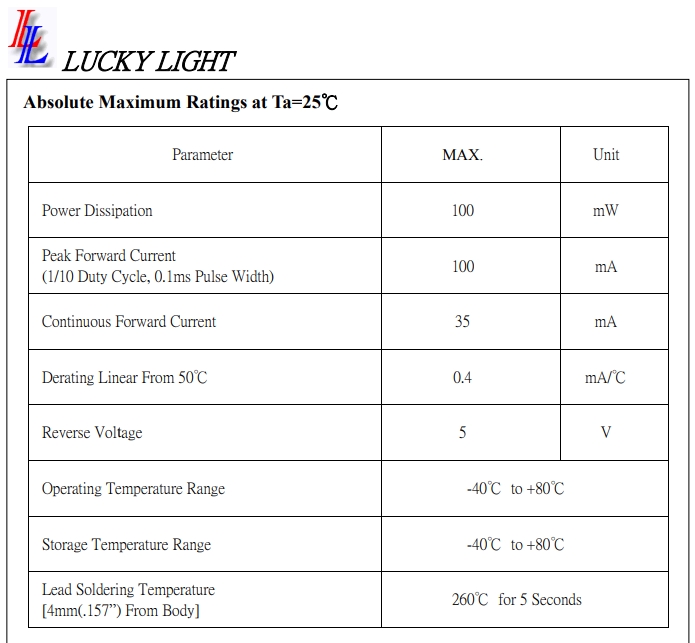
images/doku/CaravanPi-LED-Datasheet1.jpg
