spitzlbergerj/CaravanPi/images/doku/CaravanPi-LED-Datasheet2.jpg

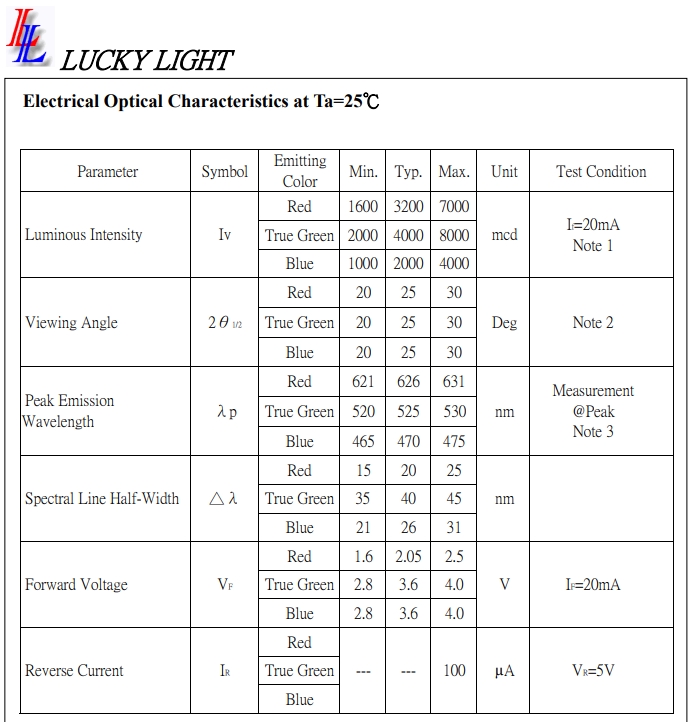
images/doku/CaravanPi-LED-Datasheet2.jpg
