spitzlbergerj/CaravanPi/images/doku/CaravanPi-LED-Datasheet3.jpg

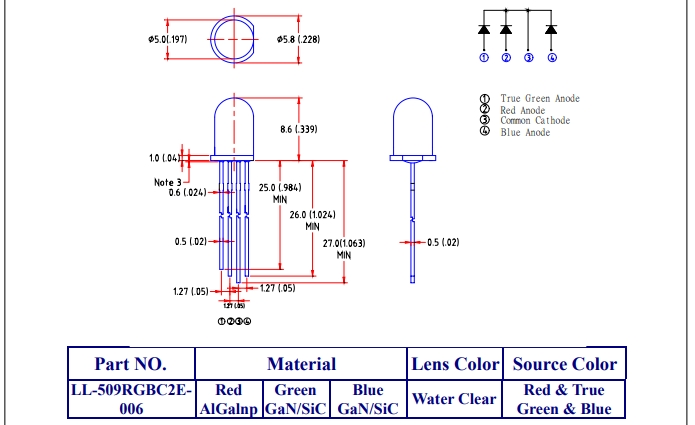
images/doku/CaravanPi-LED-Datasheet3.jpg
