spitzlbergerj/CaravanPi/images/doku/CaravanPi-LED-Einbau-Deichsel.jpg

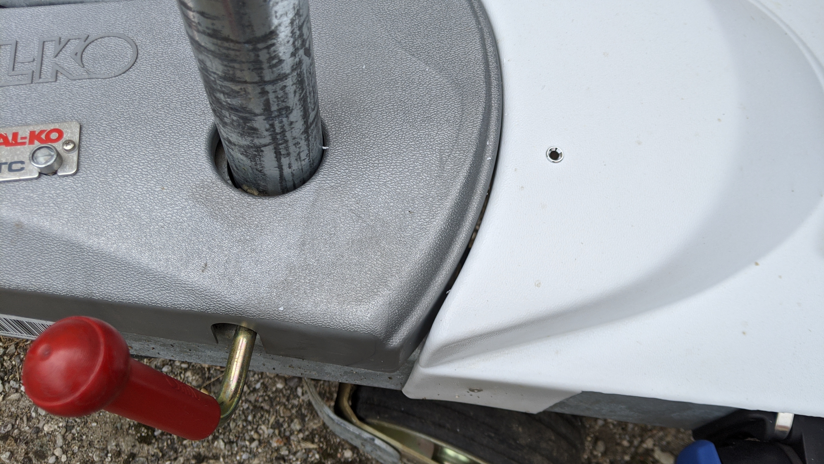
images/doku/CaravanPi-LED-Einbau-Deichsel.jpg
