spitzlbergerj/CaravanPi/images/doku/CaravanPi-LED-Einbau-Heck.jpg

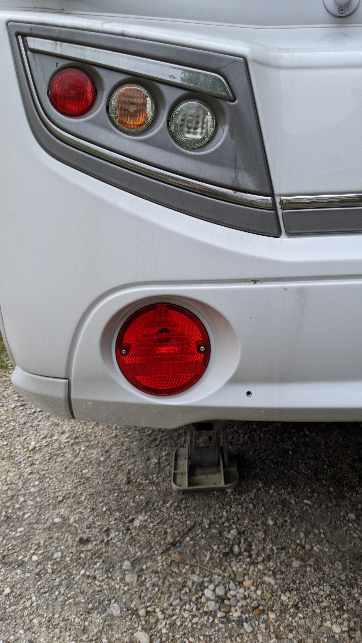
images/doku/CaravanPi-LED-Einbau-Heck.jpg
