spitzlbergerj/CaravanPi/images/doku/CaravanPi-LED-Einbau-Stecker1.jpg

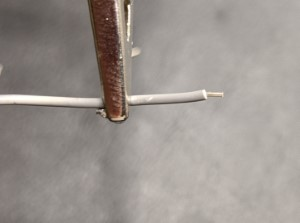
images/doku/CaravanPi-LED-Einbau-Stecker1.jpg
