spitzlbergerj/CaravanPi/images/doku/CaravanPi-LED-Einbau-Stecker2.jpg

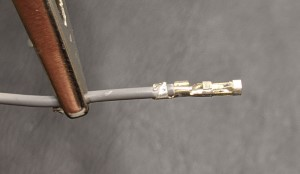
images/doku/CaravanPi-LED-Einbau-Stecker2.jpg
