spitzlbergerj/CaravanPi/images/doku/CaravanPi-LED-Einbau-Stecker3.jpg

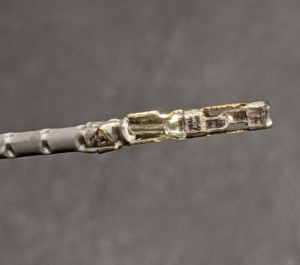
images/doku/CaravanPi-LED-Einbau-Stecker3.jpg
