spitzlbergerj/CaravanPi/images/doku/CaravanPi-LED-Einbau-Stecker4.jpg

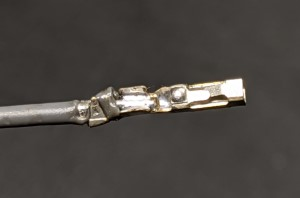
images/doku/CaravanPi-LED-Einbau-Stecker4.jpg
