spitzlbergerj/CaravanPi/images/doku/CaravanPi-LED-Einbau-Stecker5.jpg

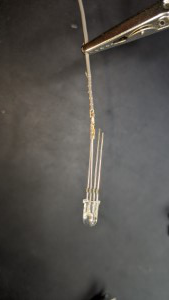
images/doku/CaravanPi-LED-Einbau-Stecker5.jpg
