spitzlbergerj/CaravanPi/images/doku/CaravanPi-LED-Einbau-Stecker-Crimp1.jpg

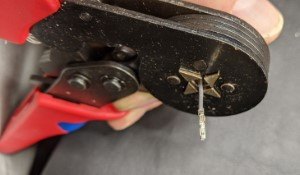
images/doku/CaravanPi-LED-Einbau-Stecker-Crimp1.jpg
