spitzlbergerj/CaravanPi/images/doku/CaravanPi-LED-Einbau-Stecker-Crimp2.jpg

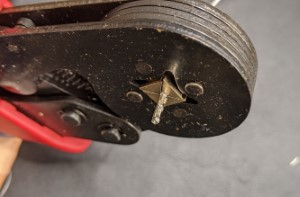
images/doku/CaravanPi-LED-Einbau-Stecker-Crimp2.jpg
