spitzlbergerj/CaravanPi/images/doku/CaravanPi-LSA-Leiste1.jpg

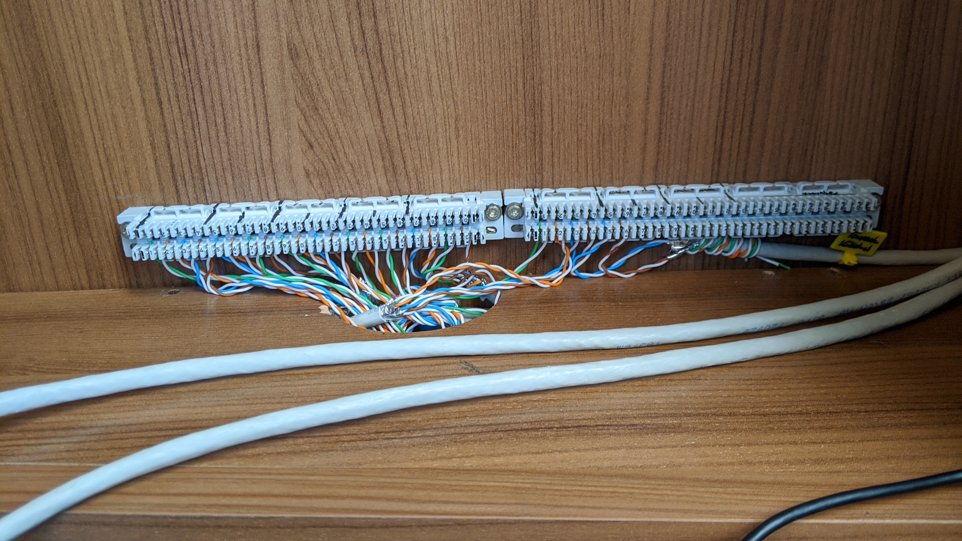
images/doku/CaravanPi-LSA-Leiste1.jpg
