spitzlbergerj/CaravanPi/images/doku/CaravanPi-LSA-Leiste2.jpg

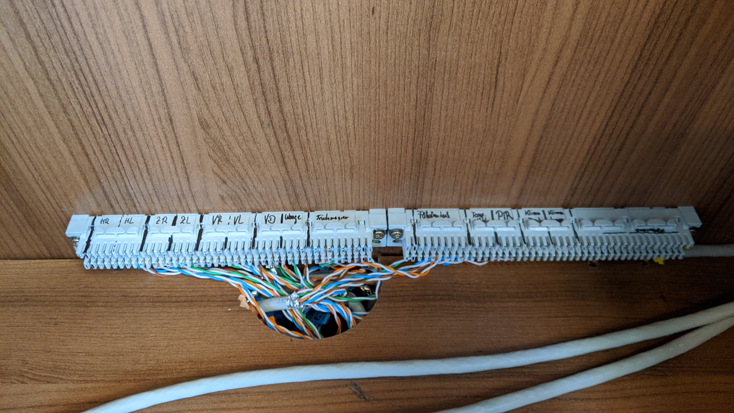
images/doku/CaravanPi-LSA-Leiste2.jpg
