spitzlbergerj/CaravanPi/images/doku/CaravanPi-LTE-Antenne-1.jpeg

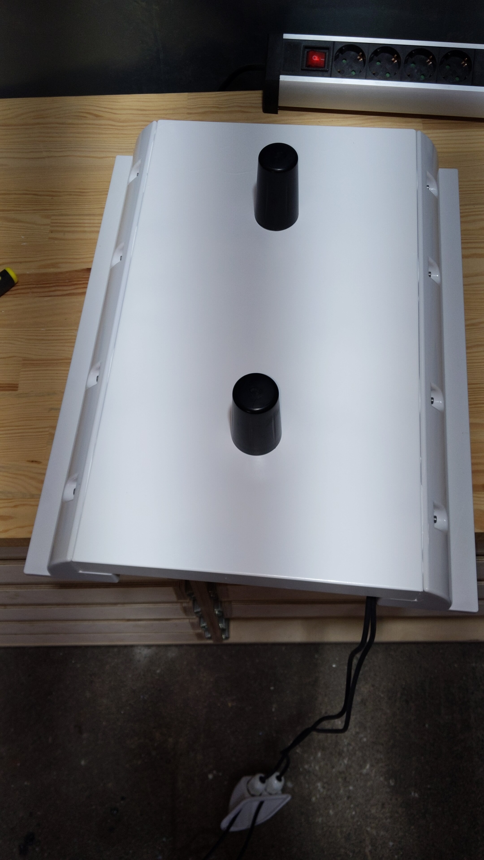
images/doku/CaravanPi-LTE-Antenne-1.jpeg
