spitzlbergerj/CaravanPi/images/doku/CaravanPi-LTE-Antenne-2.jpeg

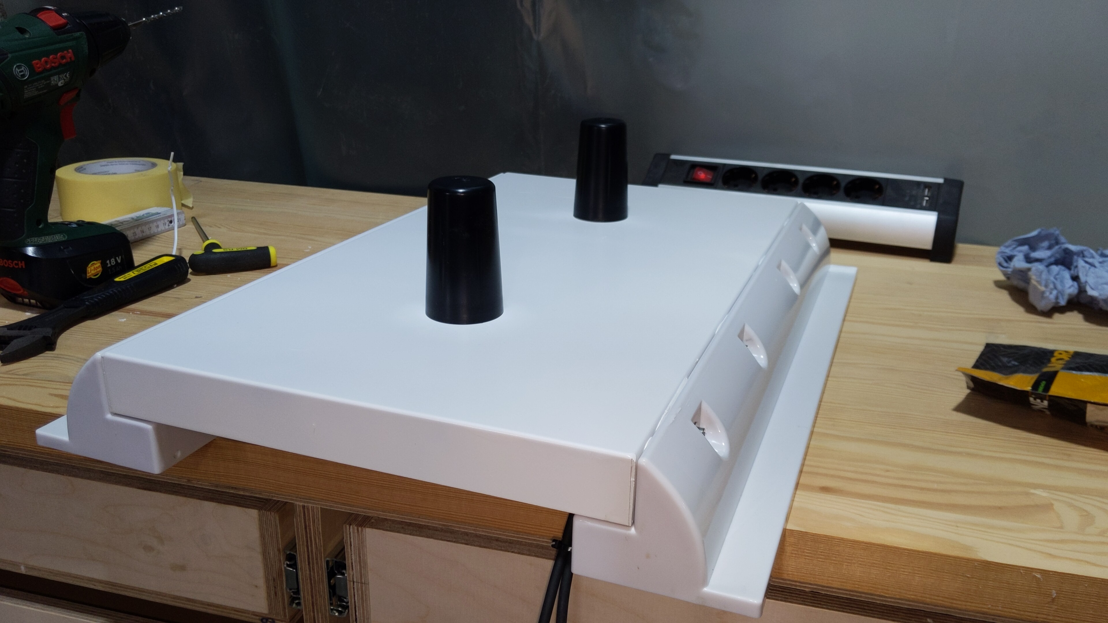
images/doku/CaravanPi-LTE-Antenne-2.jpeg
