spitzlbergerj/CaravanPi/images/doku/CaravanPi-MagicMirror-Console.jpg

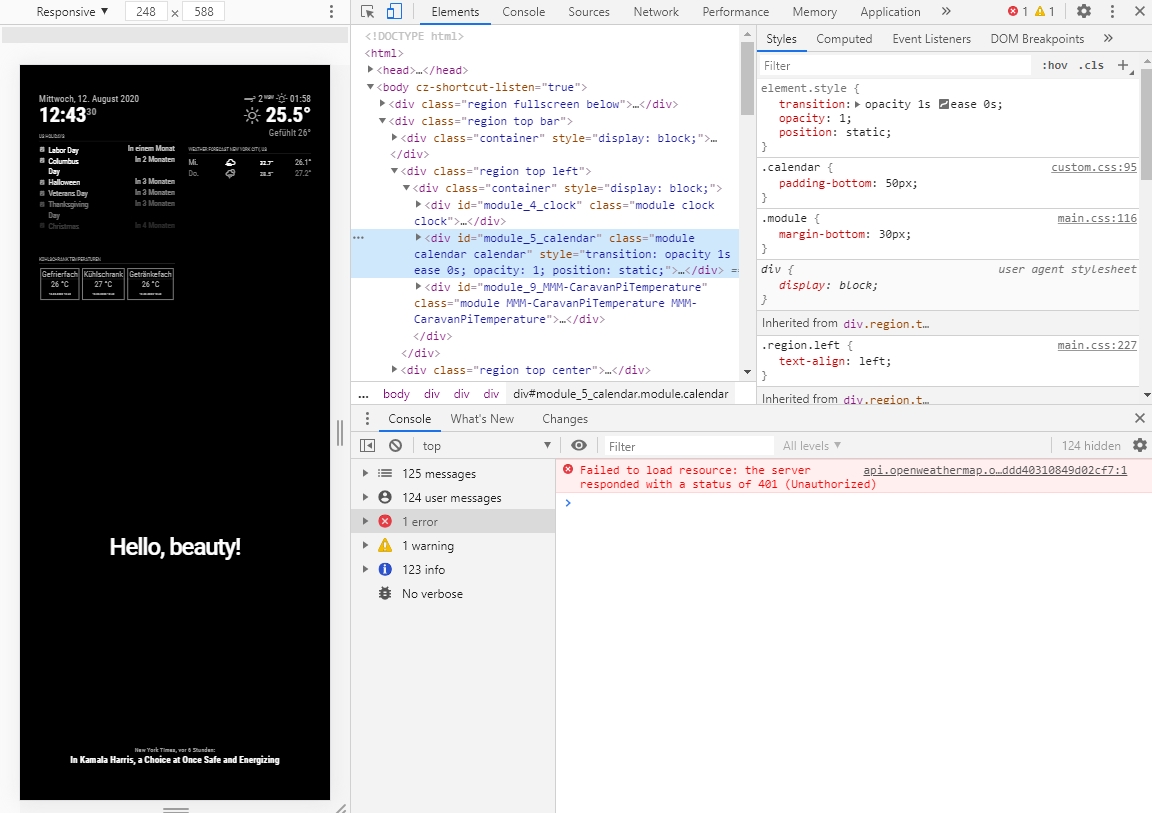
images/doku/CaravanPi-MagicMirror-Console.jpg
