spitzlbergerj/CaravanPi/images/doku/CaravanPi-MagicMirror-RemoteControl.jpg

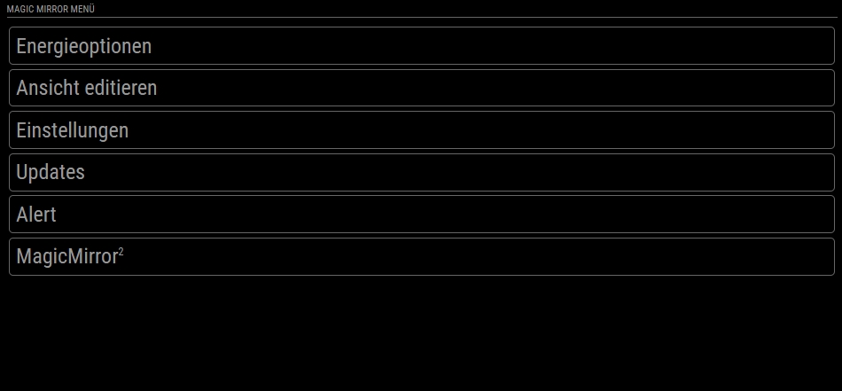
images/doku/CaravanPi-MagicMirror-RemoteControl.jpg
