spitzlbergerj/CaravanPi/images/doku/CaravanPi-MagicMirror-Untersuchen.jpg

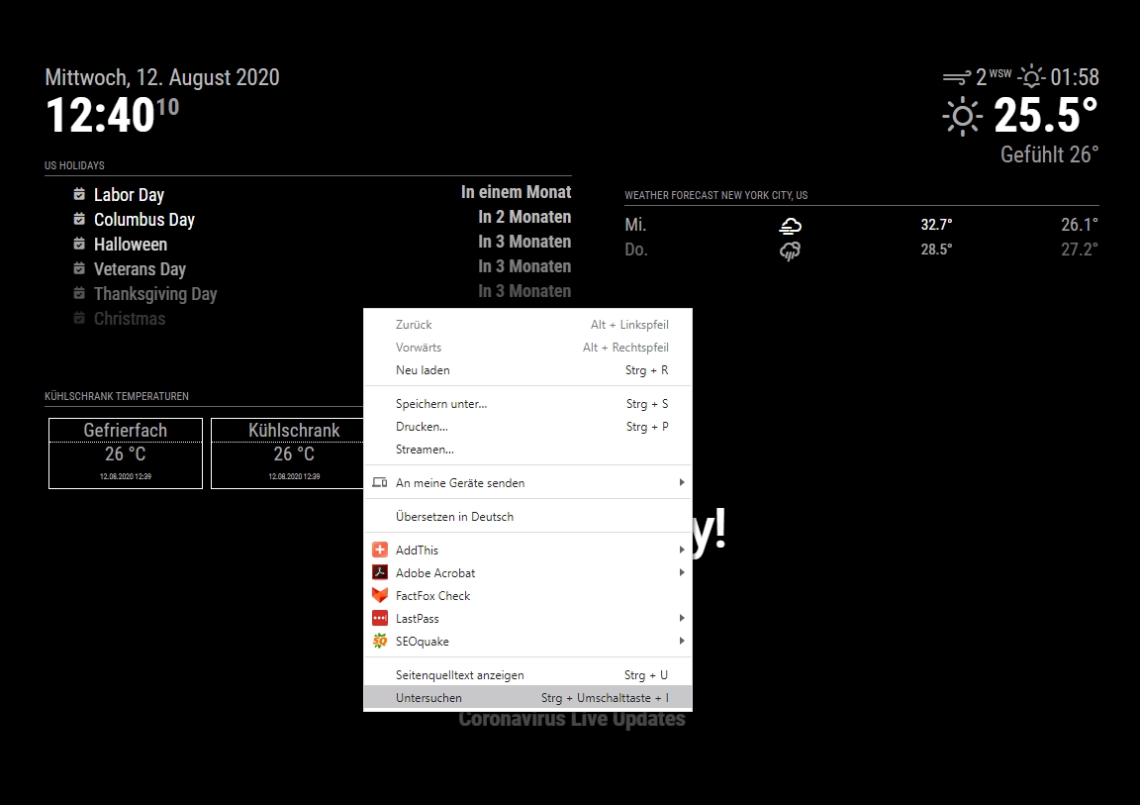
images/doku/CaravanPi-MagicMirror-Untersuchen.jpg
