spitzlbergerj/CaravanPi/images/doku/CaravanPi-MCP23017-1.jpg

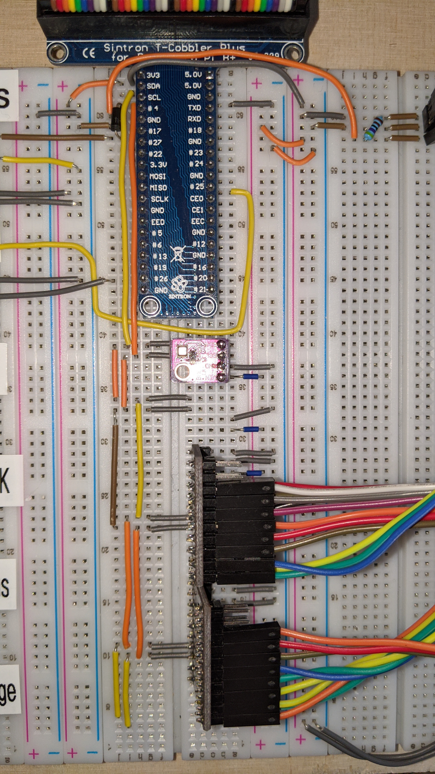
images/doku/CaravanPi-MCP23017-1.jpg
