spitzlbergerj/CaravanPi/images/doku/CaravanPi-MCP23017-3.jpg

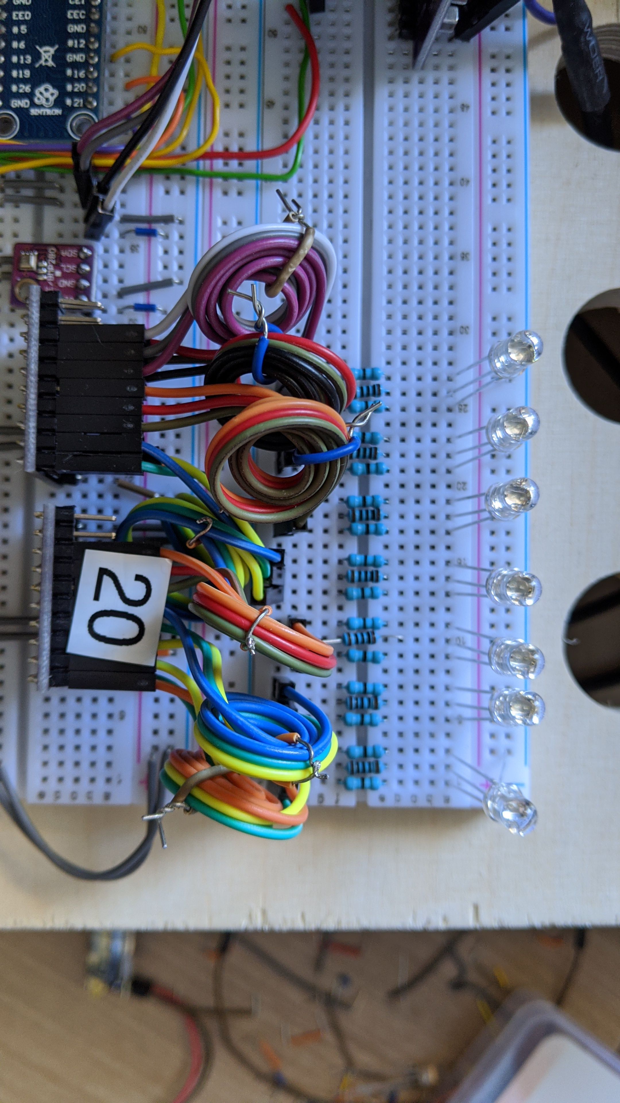
images/doku/CaravanPi-MCP23017-3.jpg
