spitzlbergerj/CaravanPi/images/doku/CaravanPi-MCP23017-4.jpg

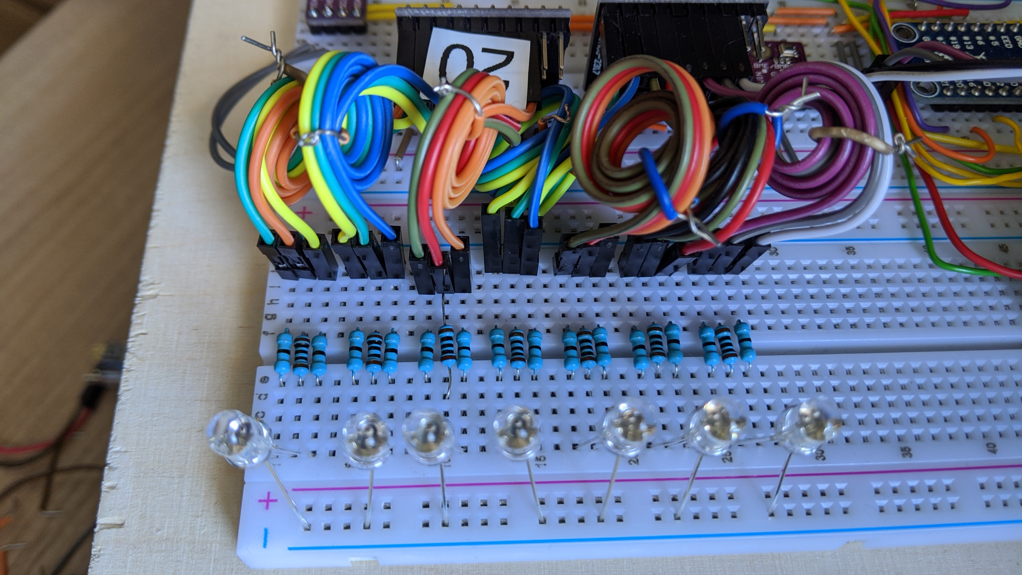
images/doku/CaravanPi-MCP23017-4.jpg
