spitzlbergerj/CaravanPi/images/doku/CaravanPi-Platine-Rückseite350.png

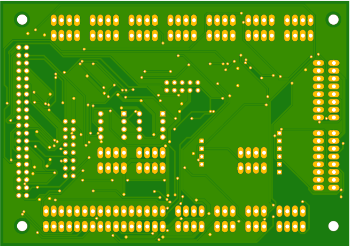
images/doku/CaravanPi-Platine-Rückseite350.png
