spitzlbergerj/CaravanPi/images/doku/CaravanPi-Platine-V2.png

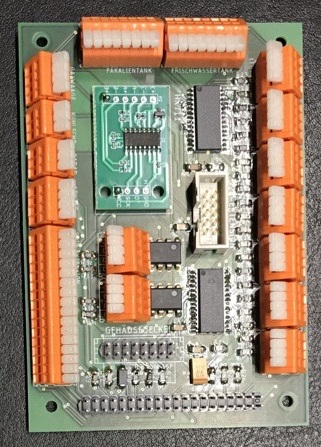
images/doku/CaravanPi-Platine-V2.png
