spitzlbergerj/CaravanPi/images/doku/CaravanPi-Platine-Vorderseite350.png

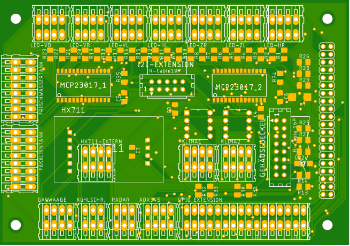
images/doku/CaravanPi-Platine-Vorderseite350.png
