spitzlbergerj/CaravanPi/images/doku/CaravanPi-Platinen-Schaltplan.png

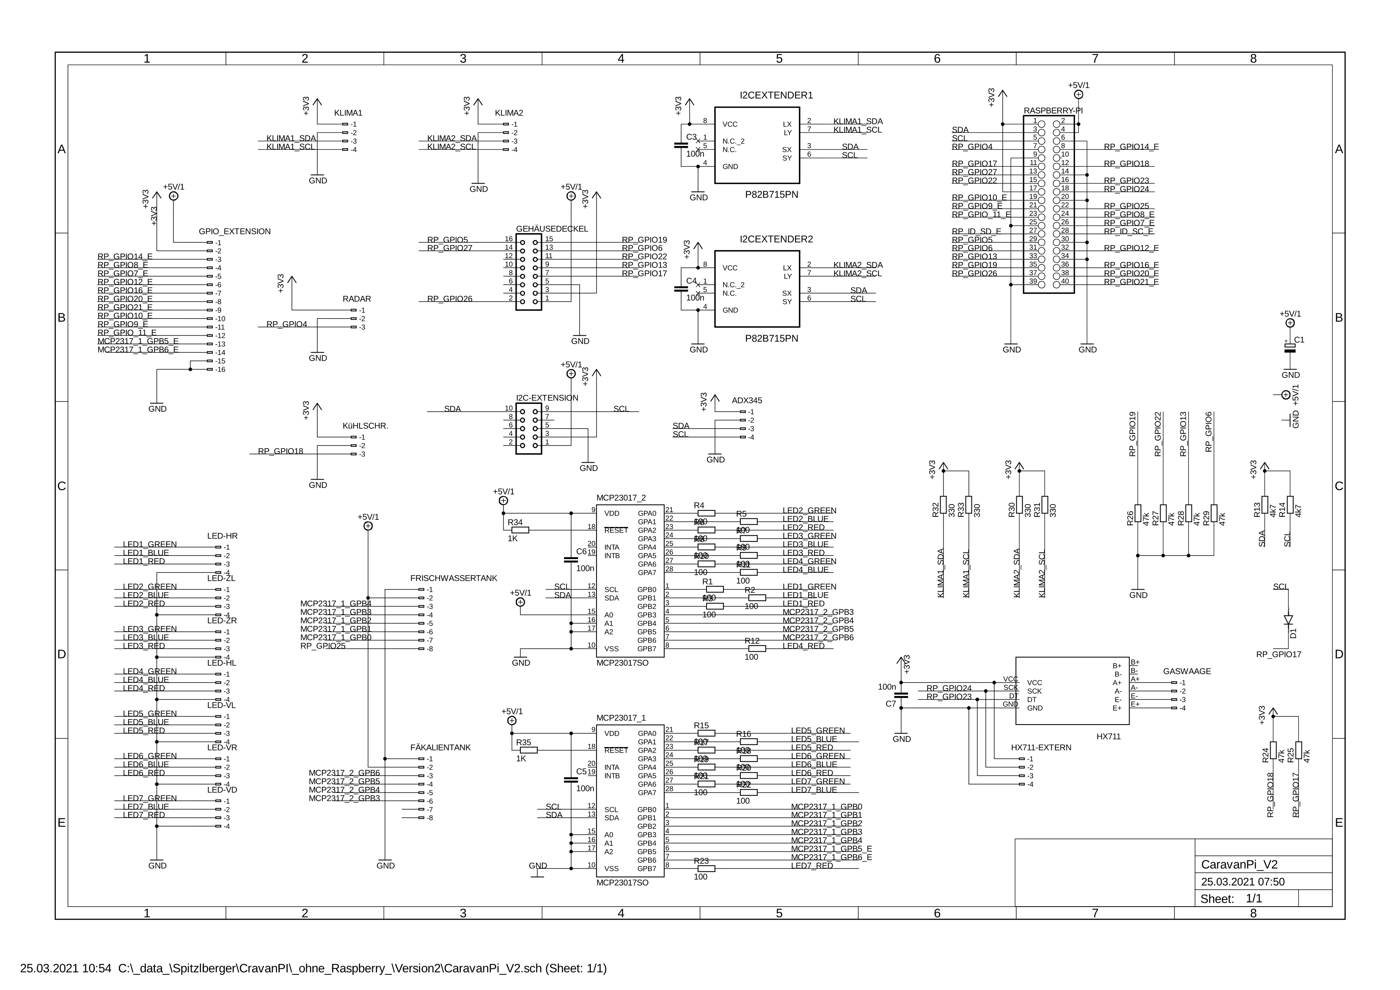
images/doku/CaravanPi-Platinen-Schaltplan.png
