spitzlbergerj/CaravanPi/images/doku/CaravanPi-Verkabelung-LSABox.jpg

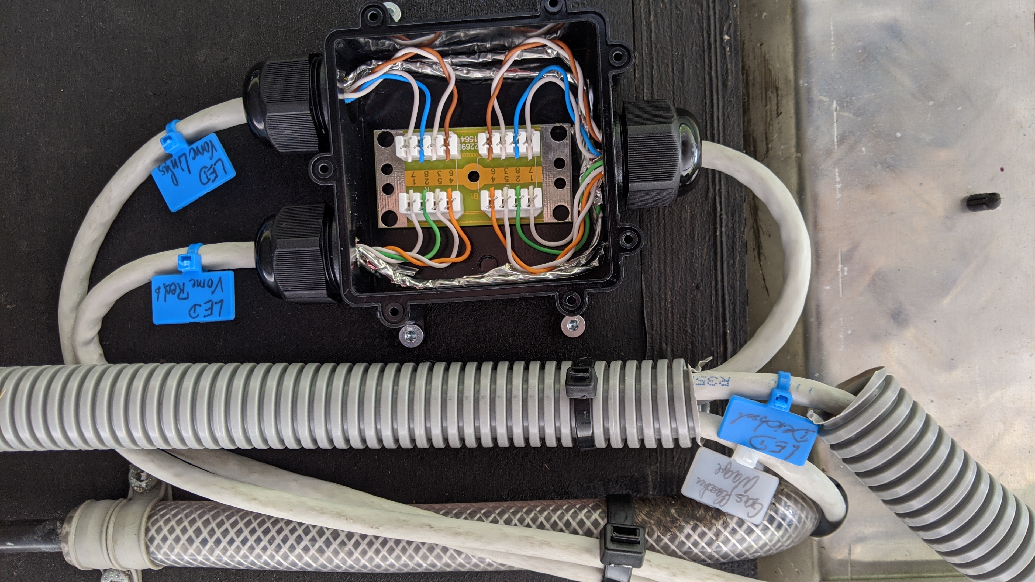
images/doku/CaravanPi-Verkabelung-LSABox.jpg
