spitzlbergerj/CaravanPi/images/doku/CaravanPi-Verzeichnisstruktur.jpg

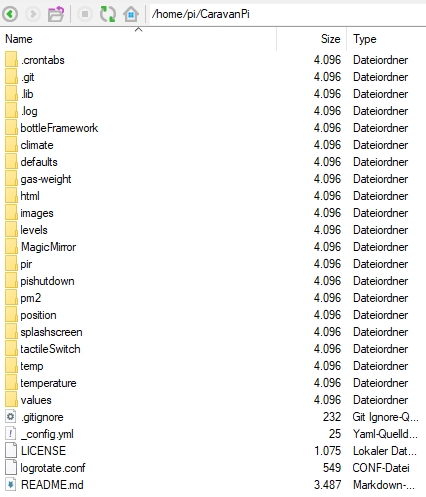
images/doku/CaravanPi-Verzeichnisstruktur.jpg
