spitzlbergerj/CaravanPi/images/doku/CaravanPiBoard-Buzzerr.jpg

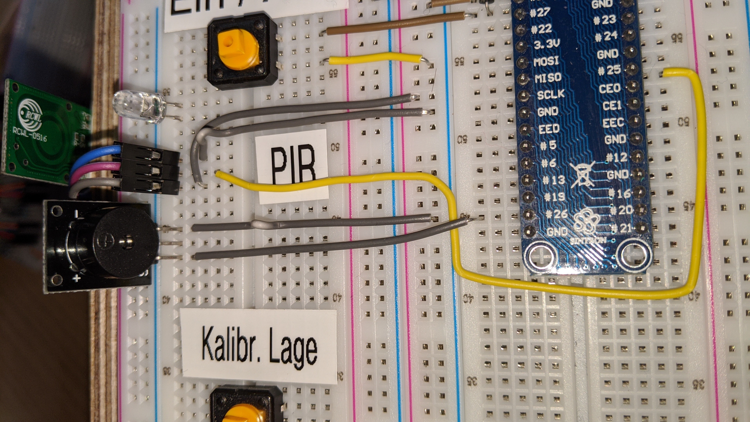
images/doku/CaravanPiBoard-Buzzerr.jpg
