spitzlbergerj/CaravanPi/images/doku/CaravanPiBoard-PIR-LED.jpg

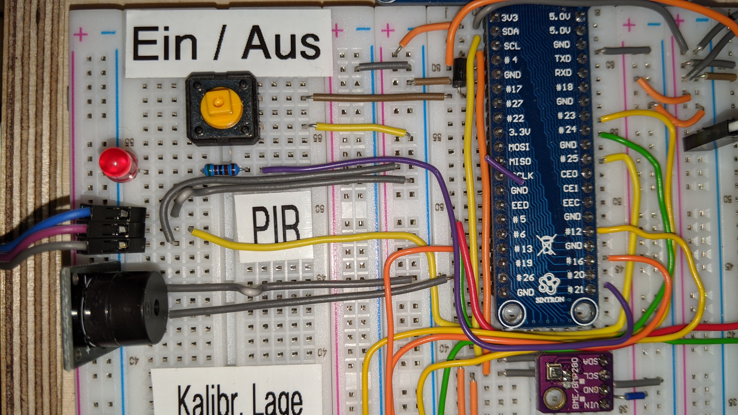
images/doku/CaravanPiBoard-PIR-LED.jpg
