spitzlbergerj/CaravanPi/images/doku/CaravanPiBoard-PIR-Sensor.jpg

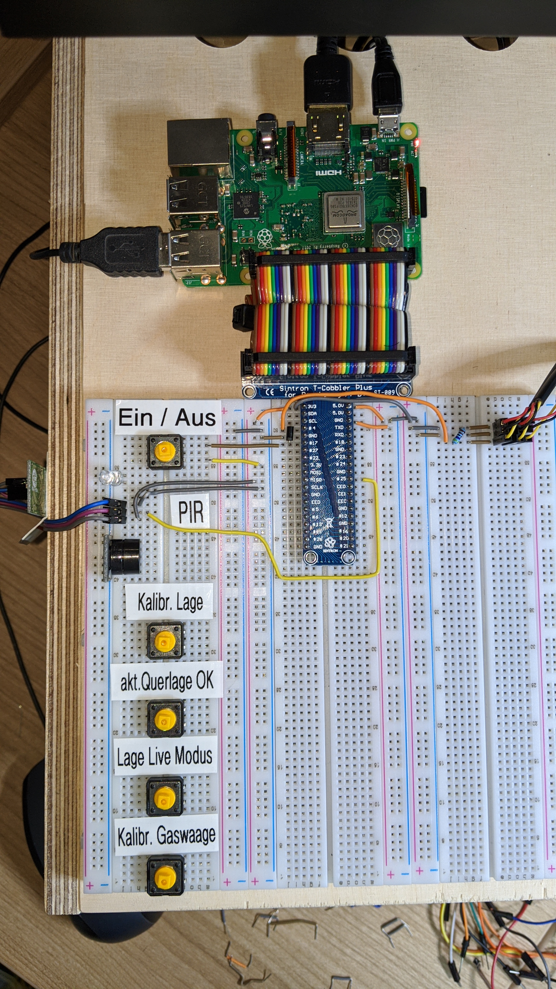
images/doku/CaravanPiBoard-PIR-Sensor.jpg
