spitzlbergerj/CaravanPi/images/doku/dometic_rmf8505.png

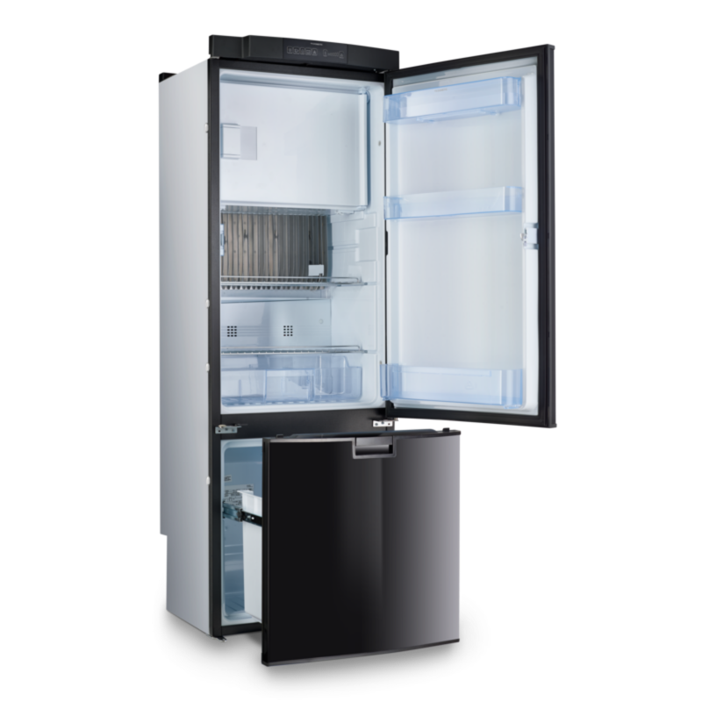
images/doku/dometic_rmf8505.png
