spitzlbergerj/CaravanPi/images/doku/i2c-extender-schaltbild.jpg

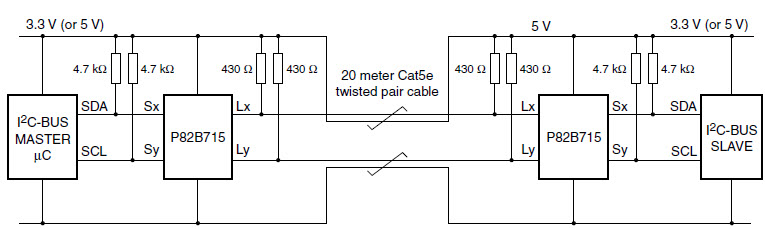
images/doku/i2c-extender-schaltbild.jpg
