spitzlbergerj/CaravanPi/images/doku/MagicMirror-Standard.jpg

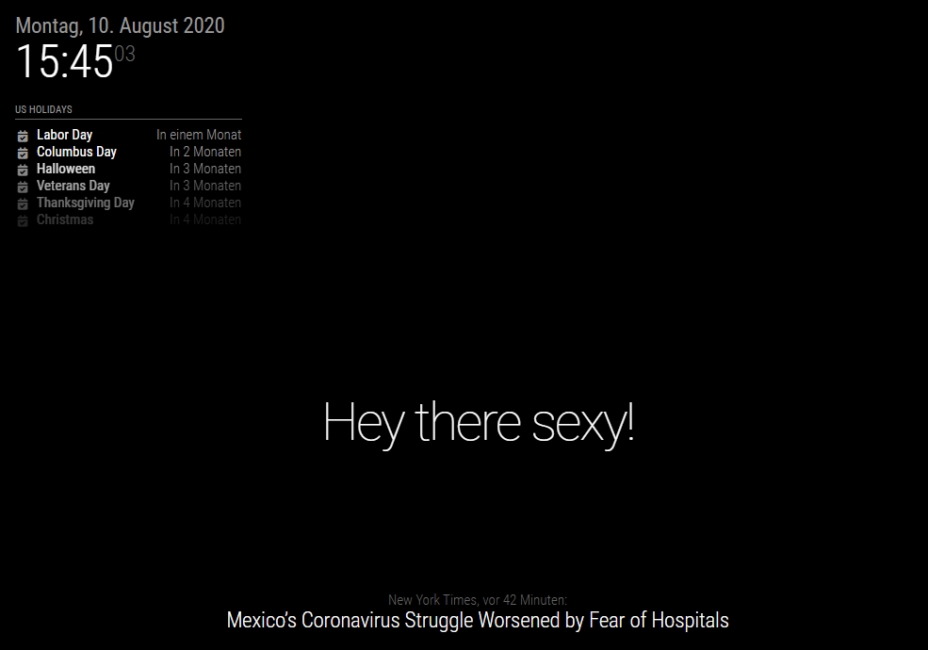
images/doku/MagicMirror-Standard.jpg
