spitzlbergerj/CaravanPi/images/doku/MMM-CaravanPiPosition-Screendump.jpg

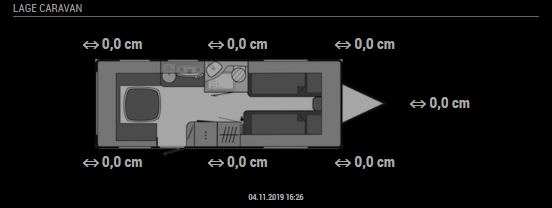
images/doku/MMM-CaravanPiPosition-Screendump.jpg
