spitzlbergerj/CaravanPi/images/doku/pfostenstecker-schematisch.jpg

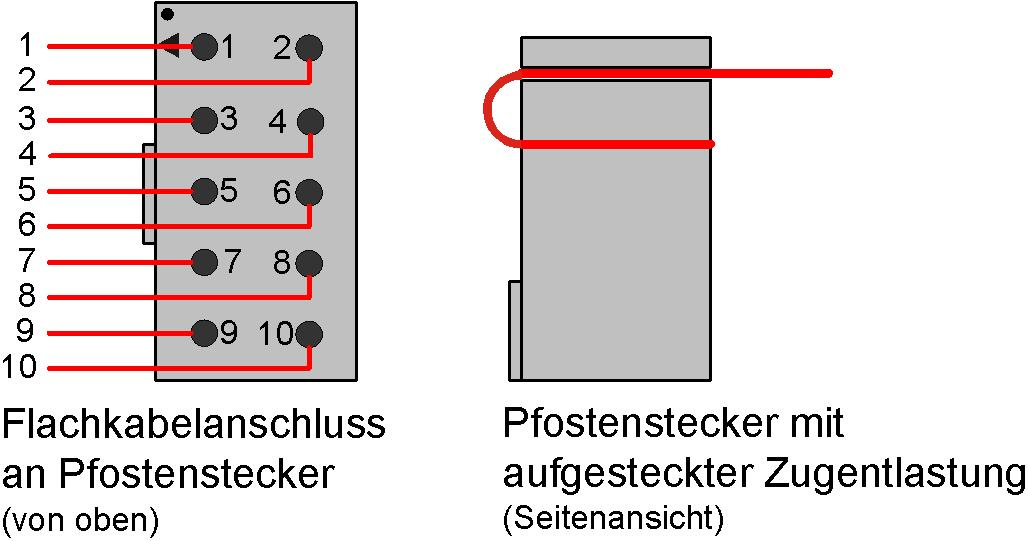
images/doku/pfostenstecker-schematisch.jpg
