spitzlbergerj/CaravanPi/images/LED-Matrix.jpg

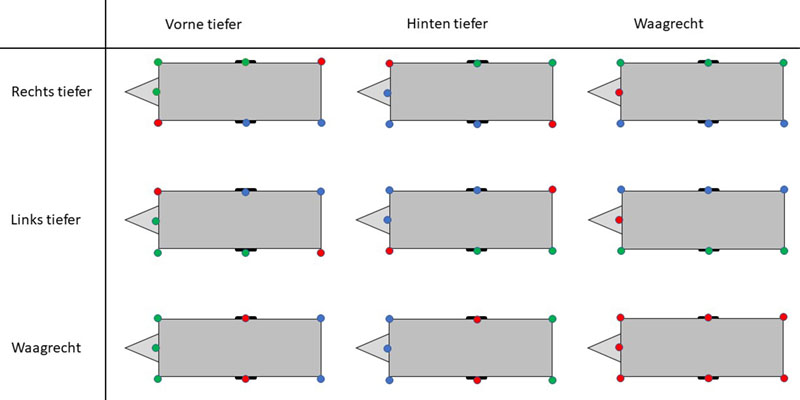
images/LED-Matrix.jpg
