spitzlbergerj/CaravanPi/circuit-board/Make-Artikel-Platinenbestückung-kostenlos.jpg

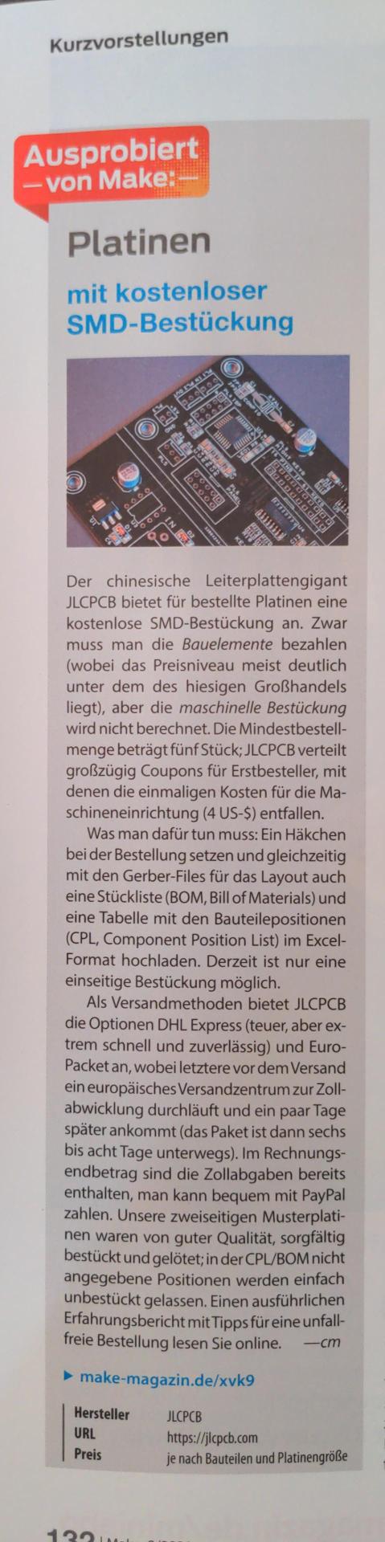
circuit-board/Make-Artikel-Platinenbestückung-kostenlos.jpg
