spitzlbergerj/CaravanPi/images/doku/testaufbau.jpg

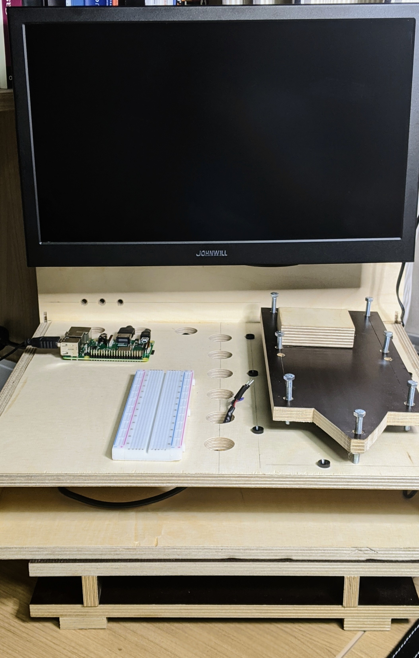
images/doku/testaufbau.jpg
