spitzlbergerj/CaravanPi/images/doku/CaravanPi-Frischwassertank-Testkabel.jpg

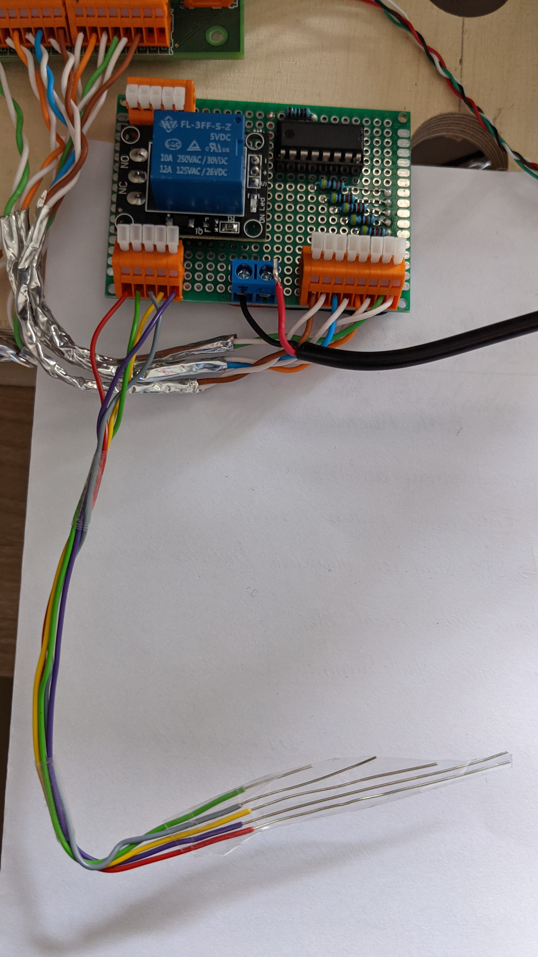
images/doku/CaravanPi-Frischwassertank-Testkabel.jpg
