spitzlbergerj/CaravanPi/images/doku/CaravanPi-Horter-Kalb-Testplatine-I2C-Extender.jpg

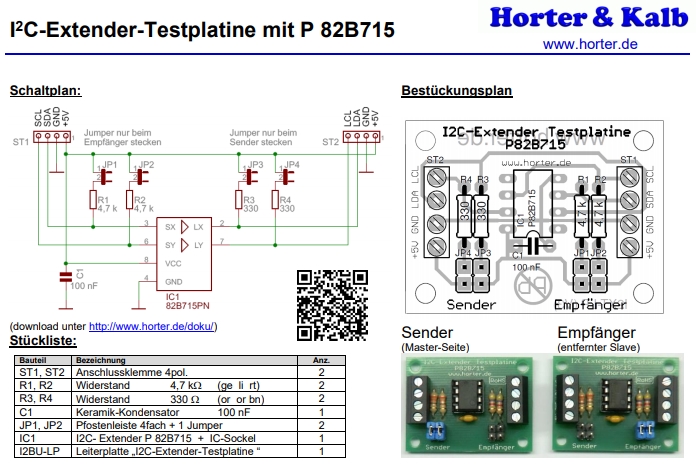
images/doku/CaravanPi-Horter-Kalb-Testplatine-I2C-Extender.jpg
