spitzlbergerj/CaravanPi/images/doku/CaravanPiTester2.jpg

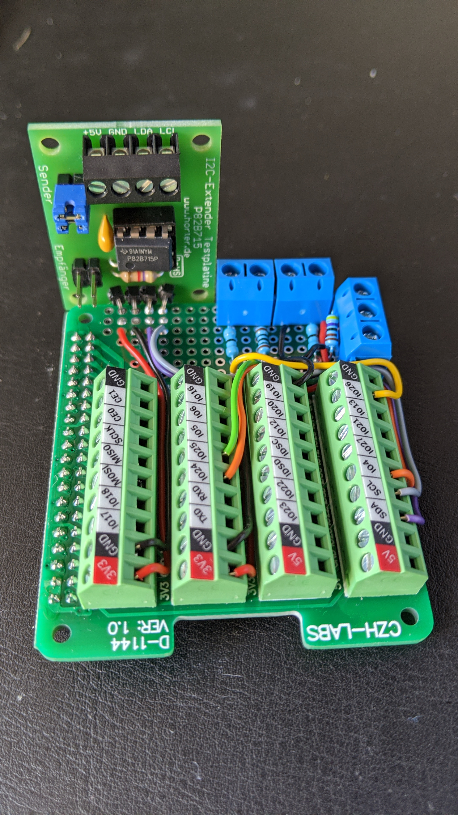
images/doku/CaravanPiTester2.jpg
