spitzlbergerj/CaravanPi/images/doku/CaravanPiTester3.jpg

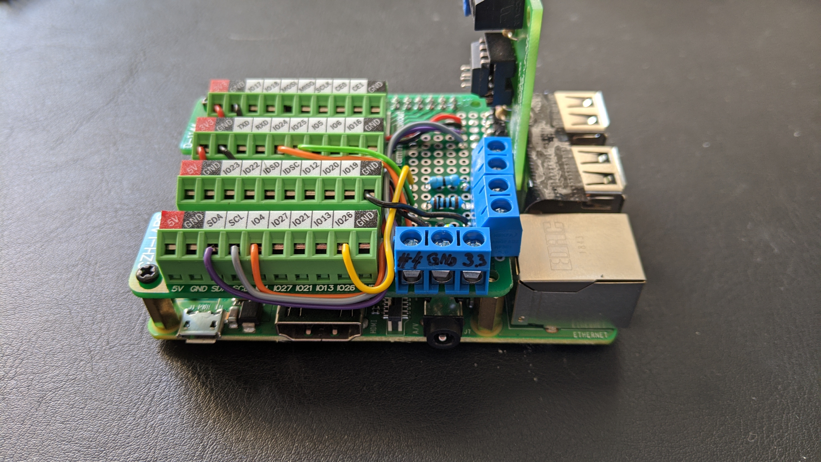
images/doku/CaravanPiTester3.jpg
