spitzlbergerj/CaravanPi/images/doku/CaravanPi-LED-Einbau-Bug.jpg

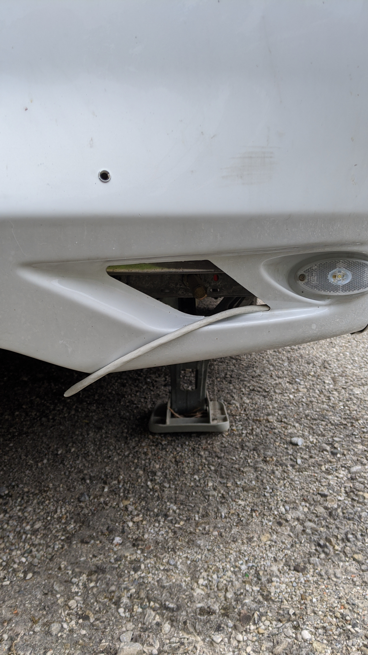
images/doku/CaravanPi-LED-Einbau-Bug.jpg
