spitzlbergerj/CaravanPi/html-flask/config_routes.py

#
#
#

import sys
import subprocess
from flask import Flask, render_template, request, redirect, url_for, flash

# -----------------------------------------------
# CaravanPi File/MARIADB/MQTT library einbinden
# -----------------------------------------------
sys.path.append('/home/pi/CaravanPi/.lib')
from CaravanPiFilesClass import CaravanPiFiles

cplib = CaravanPiFiles()



def register_config_routes(app):

	@app.route('/configs', methods=['GET', 'POST'])
	def config_home():
		return render_template('config.html')

	@app.route('/config_caravanpi', methods=['GET', 'POST'])
	def config_caravanpi():

		if request.method == 'POST':
			if 'cancel' in request.form:
				return redirect(url_for('config_home'))  # Leitet um zur `/configs`-Route

			if 'submit' in request.form:
				# Daten aus dem Formular extrahieren
				countGasScales = request.form.get('countGasScales')
				countTanks = request.form.get('countTanks')
				countClimateSensors = request.form.get('countClimateSensors')

				write2file = request.form.get('write2file')

				write2MariaDB = request.form.get('write2MariaDB')
				MariaDBhost = request.form.get('MariaDBhost')
				MariaDBuser = request.form.get('MariaDBuser')
				MariaDBpasswd = request.form.get('MariaDBpasswd')
				MariaDBdatabase = request.form.get('MariaDBdatabase')

				send2MQTT = request.form.get('send2MQTT')
				MQTTbroker = request.form.get('MQTTbroker')
				MQTTport = request.form.get('MQTTport')
				MQTTuser = request.form.get('MQTTuser')
				MQTTpassword = request.form.get('MQTTpassword')

				intervallGasscale = request.form.get('intervallGasscale')
				intervallTemp = request.form.get('intervallTemp')
				intervallClimate = request.form.get('intervallClimate')
				intervallTanks = request.form.get('intervallTanks')
				intervallPositionNormal = request.form.get('intervallPositionNormal')
				intervallRaspberry = request.form.get('intervallRaspberry')

				LiontronMACAddress = request.form.get('LiontronMACAddress')
				stromPiInstalled = request.form.get('stromPiInstalled')

				gassensorInstalled = request.form.get('gassensorInstalled')
				gassensorDigitalIn = request.form.get('gassensorDigitalIn')
				gassensorAnalogIn = request.form.get('gassensorAnalogIn')
				gassensorAlarmActive = request.form.get('gassensorAlarmActive')
				gassensorAlarmResume = request.form.get('gassensorAlarmResume')

				v230CheckInstalled = request.form.get('v230CheckInstalled')
				v230CheckADCPin = request.form.get('v230CheckADCPin')
				v230CheckAlarmActive = request.form.get('v230CheckAlarmActive')
				v230CheckAlarmResume = request.form.get('v230CheckAlarmResume')

				v12BatteryCheckInstalled = request.form.get('v12BatteryCheckInstalled')
				v12BatteryCheckADCPin = request.form.get('v12BatteryCheckADCPin')
				v12BatteryCheckAlarmActive = request.form.get('v12BatteryCheckAlarmActive')
				v12BatteryCheckAlarmResume = request.form.get('v12BatteryCheckAlarmResume')
				v12BatteryR1 = request.form.get('v12BatteryR1')
				v12BatteryR2 = request.form.get('v12BatteryR2')

				v12CarCheckInstalled = request.form.get('v12CarCheckInstalled')
				v12CarCheckADCPin = request.form.get('v12CarCheckADCPin')
				v12CarCheckAlarmActive = request.form.get('v12CarCheckAlarmActive')
				v12CarCheckAlarmResume = request.form.get('v12CarCheckAlarmResume')
				v12CarR1 = request.form.get('v12CarR1')
				v12CarR2 = request.form.get('v12CarR2')

				BuzzerGPIOPin = request.form.get('BuzzerGPIOPin')

				try:
					# Konvertierung der Daten in die richtigen Typen (z.B. in float) und einfügen in ein Dictionary
					config_dict = {
						'countGasScales': int(countGasScales) if countGasScales and 1 <= int(countGasScales) <= 2 else None,
						'countTanks': int(countTanks) if countTanks and 1 <= int(countTanks) <= 3 else None,
						'countClimateSensors': int(countClimateSensors) if countClimateSensors and 1 <= int(countClimateSensors) <= 2 else None,

						'write2file': bool(write2file) if write2file is not None else None,

						'write2MariaDB': bool(write2MariaDB) if write2MariaDB is not None else None,
						'MariaDBhost': MariaDBhost if MariaDBhost else None,
						'MariaDBuser': MariaDBuser if MariaDBuser else None,
						'MariaDBpasswd': MariaDBpasswd if MariaDBpasswd else None,
						'MariaDBdatabase': MariaDBdatabase if MariaDBdatabase else None,

						'send2MQTT': bool(send2MQTT) if send2MQTT is not None else None,
						'MQTTbroker': MQTTbroker if MQTTbroker else None,
						'MQTTport': int(MQTTport) if MQTTport else None,
						'MQTTuser': MQTTuser if MQTTuser else None,
						'MQTTpassword': MQTTpassword if MQTTpassword else None,

						'intervallGasscale': int(intervallGasscale) if intervallGasscale and 1 <= int(intervallGasscale) <= 120 else None,
						'intervallTemp': int(intervallTemp) if intervallTemp and 1 <= int(intervallTemp) <= 120 else None,
						'intervallClimate': int(intervallClimate) if intervallClimate and 1 <= int(intervallClimate) <= 120 else None,
						'intervallTanks': int(intervallTanks) if intervallTanks and 1 <= int(intervallTanks) <= 120 else None,
						'intervallPositionNormal': int(intervallPositionNormal) if intervallPositionNormal and 1 <= int(intervallPositionNormal) <= 120 else None,
						'intervallRaspberry': int(intervallRaspberry) if intervallRaspberry and 1 <= int(intervallRaspberry) <= 120 else None,

						'LiontronMACAddress': LiontronMACAddress if LiontronMACAddress else None,
						'stromPiInstalled': bool(stromPiInstalled) if stromPiInstalled is not None else None,

						'gassensorInstalled': bool(gassensorInstalled) if gassensorInstalled is not None else None,
						'gassensorDigitalIn': int(gassensorDigitalIn) if gassensorDigitalIn and 0 <= int(gassensorDigitalIn) <= 40 else None,
						'gassensorAnalogIn': int(gassensorAnalogIn) if gassensorAnalogIn and 0 <= int(gassensorAnalogIn) <= 3 else None,
						'gassensorAlarmActive': bool(gassensorAlarmActive) if gassensorAlarmActive is not None else None,
						'gassensorAlarmResume': bool(gassensorAlarmResume) if gassensorAlarmResume is not None else None,

						'v230CheckInstalled': bool(v230CheckInstalled) if v230CheckInstalled is not None else None,
						'v230CheckADCPin': int(v230CheckADCPin) if v230CheckADCPin and 0 <= int(v230CheckADCPin) <= 40 else None,
						'v230CheckAlarmActive': bool(v230CheckAlarmActive) if v230CheckAlarmActive is not None else None,
						'v230CheckAlarmResume': bool(v230CheckAlarmResume) if v230CheckAlarmResume is not None else None,

						'v12BatteryCheckInstalled': bool(v12BatteryCheckInstalled) if v12BatteryCheckInstalled is not None else None,
						'v12BatteryCheckADCPin': int(v12BatteryCheckADCPin) if v12BatteryCheckADCPin and 0 <= int(v12BatteryCheckADCPin) <= 40 else None,
						'v12BatteryCheckAlarmActive': bool(v12BatteryCheckAlarmActive) if v12BatteryCheckAlarmActive is not None else None,
						'v12BatteryCheckAlarmResume': bool(v12BatteryCheckAlarmResume) if v12BatteryCheckAlarmResume is not None else None,
						'v12BatteryR1': int(v12BatteryR1) if v12BatteryR1 and 0 <= int(v12BatteryR1) <= 10000000 else None,
						'v12BatteryR2': int(v12BatteryR2) if v12BatteryR2 and 0 <= int(v12BatteryR2) <= 10000000 else None,

						'v12CarCheckInstalled': bool(v12CarCheckInstalled) if v12CarCheckInstalled is not None else None,
						'v12CarCheckADCPin': int(v12CarCheckADCPin) if v12CarCheckADCPin and 0 <= int(v12CarCheckADCPin) <= 40 else None,
						'v12CarCheckAlarmActive': bool(v12CarCheckAlarmActive) if v12CarCheckAlarmActive is not None else None,
						'v12CarCheckAlarmResume': bool(v12CarCheckAlarmResume) if v12CarCheckAlarmResume is not None else None,
						'v12CarR1': int(v12CarR1) if v12CarR1 and 0 <= int(v12CarR1) <= 10000000 else None,
						'v12CarR2': int(v12CarR2) if v12CarR2 and 0 <= int(v12CarR2) <= 10000000 else None,

						'BuzzerGPIOPin': int(BuzzerGPIOPin) if BuzzerGPIOPin and 0 <= int(BuzzerGPIOPin) <= 40 else None,

					}
				except ValueError:
					# Behandlung von Konvertierungsfehlern, z.B. wenn ein Wert nicht in den erwarteten Typ konvertiert werden kann
					flash('Fehler in Wertebehandlung')
					config_dict = {}
					pass

				print(config_dict)

				# Aufruf der Funktion zum Schreiben der Daten
				cplib.writeCaravanPiDefaults(config_dict)
				flash('Die Werte wurden erfolgreich gespeichert') 

			return redirect(url_for('config_caravanpi'))

		caravanpiDefaults = cplib.readCaravanPiDefaults()
		print(caravanpiDefaults)
		if caravanpiDefaults is None:
			caravanpiDefaults = {}
		return render_template('config_caravanpi.html', caravanpiDefaults=caravanpiDefaults)
	

	@app.route('/config_dimension_caravan', methods=['GET', 'POST'])
	def config_dimension_caravan():

		if request.method == 'POST':
			if 'cancel' in request.form:
				return redirect(url_for('config_home'))  # Leitet um zur `/configs`-Route

			if 'submit' in request.form:
				# Daten aus dem Formular extrahieren
				lengthOverAll = request.form.get('lengthOverAll')
				widthOverAll = request.form.get('widthOverAll')
				lengthBody = request.form.get('lengthBody')

				print(lengthOverAll, widthOverAll, lengthBody)

				# Konvertierung der Daten in die richtigen Typen (z.B. in float)
				try:
					lengthOverAll = int(lengthOverAll) if lengthOverAll else None
					widthOverAll = int(widthOverAll) if widthOverAll else None
					lengthBody = int(lengthBody) if lengthBody else None
				except ValueError:
					# Behandlung von Konvertierungsfehlern
					flash('Fehler in Wertebehandlung')
					pass

				# Aufruf der Funktion zum Schreiben der Daten
				cplib.writeDimensions(lengthOverAll, widthOverAll, lengthBody)
				flash('Die Werte wurden erfolgreich gespeichert') 

			return redirect(url_for('config_dimension_caravan'))

		dimensions_tuple = cplib.readDimensions()
		print(dimensions_tuple)
		if dimensions_tuple is None:
			dimensions = {}
		else:
			# Umwandlung des Tupels in ein Dictionary
			dimensions = {
				'lengthOverAll': dimensions_tuple[0],
				'widthOverAll': dimensions_tuple[1],
				'lengthBody': dimensions_tuple[2]
			}
		return render_template('config_dimension_caravan.html', dimensions=dimensions)

	@app.route('/config_lagesensor', methods=['GET', 'POST'])
	def config_lagesensor():

		if request.method == 'POST':
			if 'cancel' in request.form:
				return redirect(url_for('config_home'))  # Leitet um zur `/configs`-Route

			if 'submit' in request.form:
				# Daten aus dem Formular extrahieren
				adjustX = request.form.get('adjustX')
				adjustY = request.form.get('adjustY')
				adjustZ = request.form.get('adjustZ')
				toleranceX = request.form.get('toleranceX')
				toleranceY = request.form.get('toleranceY')
				approximationX = request.form.get('approximationX')
				approximationY = request.form.get('approximationY')
				distRight = request.form.get('distRight')
				distFront = request.form.get('distFront')
				distAxis = request.form.get('distAxis')

				# Konvertierung der Daten in die richtigen Typen (z.B. in float)
				try:
					adjustX = float(adjustX) if adjustX else None
					adjustY = float(adjustY) if adjustY else None
					adjustZ = float(adjustZ) if adjustZ else None
					toleranceX = float(toleranceX) if toleranceX else None
					toleranceY = float(toleranceY) if toleranceY else None
					approximationX = float(approximationX) if approximationX else None
					approximationY = float(approximationY) if approximationY else None
					distRight = int(distRight) if distRight else None
					distFront = int(distFront) if distFront else None
					distAxis = int(distAxis) if distAxis else None

				except ValueError:
					# Behandlung von Konvertierungsfehlern
					flash('Fehler in Wertebehandlung')
					pass

				# Aufruf der Funktion zum Schreiben der Daten
				cplib.writeAdjustment(adjustX, adjustY, adjustZ, toleranceX, toleranceY, approximationX, approximationY, distRight, distFront, distAxis)

				flash('Die Werte wurden erfolgreich gespeichert') 

			return redirect(url_for('config_lagesensor'))

		lagesensor_tuple = cplib.readAdjustment()
		print(lagesensor_tuple)
		if lagesensor_tuple is None:
			lagesensor = {}
		else:
			# Umwandlung des Tupels in ein Dictionary
			lagesensor = {
				'adjustX': lagesensor_tuple[0],
				'adjustY': lagesensor_tuple[1],
				'adjustZ': lagesensor_tuple[2],
				'toleranceX': lagesensor_tuple[3],
				'toleranceY': lagesensor_tuple[4],
				'approximationX': lagesensor_tuple[5],
				'approximationY': lagesensor_tuple[6],
				'distRight': lagesensor_tuple[7],
				'distFront': lagesensor_tuple[8],
				'distAxis': lagesensor_tuple[9]
			}
		return render_template('config_lagesensor_default.html', lagesensor=lagesensor)

	@app.route('/config_gaswaage', methods=['GET', 'POST'])
	def config_gaswaage():

		# Ermitteln der Anzahl der Gasflaschenwaagen
		anzWaagen = int(cplib.readCaravanPiConfigItem("caravanpiDefaults/countGasScales") or 1)

		print(f'Waagen: {anzWaagen}')

		if request.method == 'POST':
			if 'cancel' in request.form:
				return redirect(url_for('config_home'))  # Leitet um zur `/configs`-Route

			if 'submit' in request.form:
				for i in range(1, anzWaagen + 1):
					# Daten aus dem Formular extrahieren, spezifisch für jede Waage
					leergewicht = request.form.get(f'leergewicht_{i}')
					gasgewicht = request.form.get(f'gasgewicht_{i}')
					gpioHX711Dout = request.form.get(f'gpioHX711Dout_{i}')
					gpioHX711Sck = request.form.get(f'gpioHX711Sck_{i}')
					channelHX711 = request.form.get(f'channelHX711_{i}')
					refUnitHX711 = request.form.get(f'refUnitHX711_{i}')

					try:
						leergewicht = int(leergewicht) if leergewicht else None
						gasgewicht = int(gasgewicht) if gasgewicht else None
						gpioHX711Dout = int(gpioHX711Dout) if gpioHX711Dout and 1 <= int(gpioHX711Dout) <= 40 else None
						gpioHX711Sck = int(gpioHX711Sck) if gpioHX711Sck and 1 <= int(gpioHX711Sck) <= 40 else None
						channelHX711 = channelHX711 if channelHX711 in ['A', 'B'] else None
						refUnitHX711 = float(refUnitHX711) if refUnitHX711 else None
					except ValueError:
						# Behandlung von Konvertierungsfehlern
						flash(f'Fehler in Wertebehandlung für Waage {i}')
						continue

					# Aufruf der Funktion zum Schreiben der Daten, spezifisch für jede Waage
					cplib.writeGasScale(i, leergewicht, gasgewicht, gpioHX711Dout, gpioHX711Sck, channelHX711, refUnitHX711)
					flash(f'Die Werte für Waage {i} wurden erfolgreich gespeichert')

			return redirect(url_for('config_gaswaage'))

		gaswaage_tuples = []

		for i in range(1, anzWaagen + 1):
			gaswaage_tuple = cplib.readGasScale(i)
			print(i, gaswaage_tuple)

			if gaswaage_tuple is None:
				gaswaage_tuple = (1, 1, 1, 1, 'X', 0.0)

			# Umwandlung des Tupels in ein Dictionary und Hinzufügen zum Array
			gaswaage = {
				'leergewicht': gaswaage_tuple[0],
				'gasgewicht': gaswaage_tuple[1],
				'gpioHX711Dout': gaswaage_tuple[2],
				'gpioHX711Sck': gaswaage_tuple[3],
				'channelHX711': gaswaage_tuple[4],
				'refUnitHX711': gaswaage_tuple[5],
			}
			gaswaage_tuples.append(gaswaage)
	
		return render_template('config_gaswaage.html', gaswaagen=gaswaage_tuples, anzWaagen=anzWaagen)

	@app.route('/config_tanks', methods=['GET', 'POST'])
	def config_tanks():

		# Ermitteln der Anzahl der Gasflaschenwaagen
		anzTanks = int(cplib.readCaravanPiConfigItem("caravanpiDefaults/countTanks") or 1)

		print(f'Tanks: {anzTanks}')

		if request.method == 'POST':
			if 'cancel' in request.form:
				return redirect(url_for('config_home'))  # Leitet um zur `/configs`-Route

			if 'submit' in request.form:
				for i in range(1, anzTanks + 1):
					# Daten aus dem Formular extrahieren, spezifisch für jede Waage
					level1 = request.form.get(f'level1_{i}')
					level2 = request.form.get(f'level2_{i}')
					level3 = request.form.get(f'level3_{i}')
					level4 = request.form.get(f'level4_{i}')

					try:
						level1 = float(level1) if level1 else None
						level2 = float(level2) if level2 else None
						level3 = float(level3) if level3 else None
						level4 = float(level4) if level4 else None
					except ValueError:
						# Behandlung von Konvertierungsfehlern
						flash(f'Fehler in Wertebehandlung für Tank {i}')
						continue

					# Aufruf der Funktion zum Schreiben der Daten, spezifisch für jede Waage
					cplib.writeFillLevels(i, level1, level2, level3, level4)
					flash(f'Die Werte für Tank {i} wurden erfolgreich gespeichert')

			return redirect(url_for('config_tanks'))

		tank_tuples = []

		for i in range(1, anzTanks + 1):
			tank_tuple = cplib.readFillLevels(i)
			print(i, tank_tuple)
			if tank_tuple is None:
				tank_tuple = (0.0, 0.0, 0.0, 0.0)

			# Umwandlung des Tupels in ein Dictionary und Hinzufügen zum Array
			tank = {
				'level1': tank_tuple[0],
				'level2': tank_tuple[1],
				'level3': tank_tuple[2],
				'level4': tank_tuple[3],
			}
			tank_tuples.append(tank)
	
		return render_template('config_tanks.html', tanks=tank_tuples, anzTanks=anzTanks)

	@app.route('/config_voltage', methods=['GET', 'POST'])
	def config_voltage():

		if request.method == 'POST':
			if 'cancel' in request.form:
				return redirect(url_for('config_home'))  # Leitet um zur `/configs`-Route

			if 'submit' in request.form:
				# Daten aus dem Formular extrahieren, spezifisch für jede Waage
				level1 = request.form.get('level1')
				level2 = request.form.get('level2')
				level3 = request.form.get('level3')

				try:
					level1 = float(level1) if level1 else None
					level2 = float(level2) if level2 else None
					level3 = float(level3) if level3 else None
				except ValueError:
					# Behandlung von Konvertierungsfehlern
					flash('Fehler in Wertebehandlung')
					pass

				# Aufruf der Funktion zum Schreiben der Daten, spezifisch für jede Waage
				cplib.writeVoltageLevels(level1, level2, level3)
				flash(f'Die Werte für die Batterie Level wurden erfolgreich gespeichert')

			return redirect(url_for('config_voltage'))

		batterie_tuple = cplib.readVoltageLevels()
		print(batterie_tuple)
		if batterie_tuple is None:
			batterie_tuple = (0.0, 0.0, 0.0)

		# Umwandlung des Tupels in ein Dictionary und Hinzufügen zum Array
		batterie = {
			'level1': batterie_tuple[0],
			'level2': batterie_tuple[1],
			'level3': batterie_tuple[2],
		}
	
		return render_template('config_voltage.html', batterie=batterie)
