spitzlbergerj/CaravanPi/images/doku/CaravanPi-LED-Einbau-Stecker.jpg

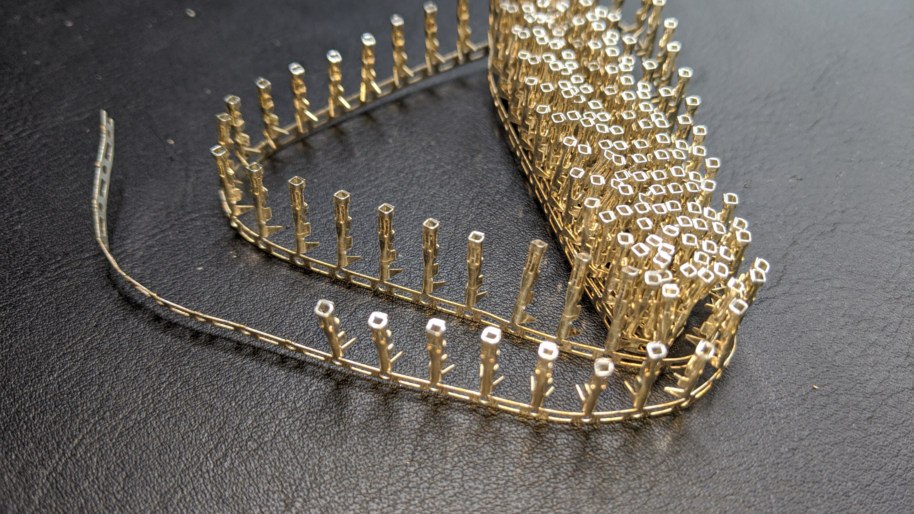
images/doku/CaravanPi-LED-Einbau-Stecker.jpg
