spitzlbergerj/CaravanPi/images/doku/CaravanPiTester1.jpg

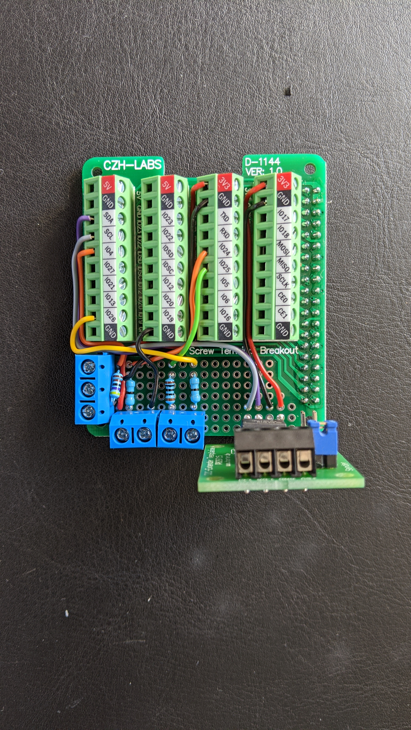
images/doku/CaravanPiTester1.jpg
